kreini/J-r-s/PosTracker/Pályamunka/Grafikonok/Autokorreláció.docx

A képen képernyőkép, madár látható Automatikusan generált leírás
