kreini/J-r-s/PosTracker/Pályamunka/Grafikonok/Derék spline.docx

A képen képernyőkép látható Automatikusan generált leírás
