kreini/J-r-s/PosTracker/Pályamunka/Grafikonok/Nyers.docx

A képen képernyőkép látható Automatikusan generált leírás
A képen étel látható Automatikusan generált leírás
A képen képernyőkép látható Automatikusan generált leírás
