kreini/J-r-s/PosTracker/Pályamunka/Műszaki rajzok/Műszaki rajzok.docx

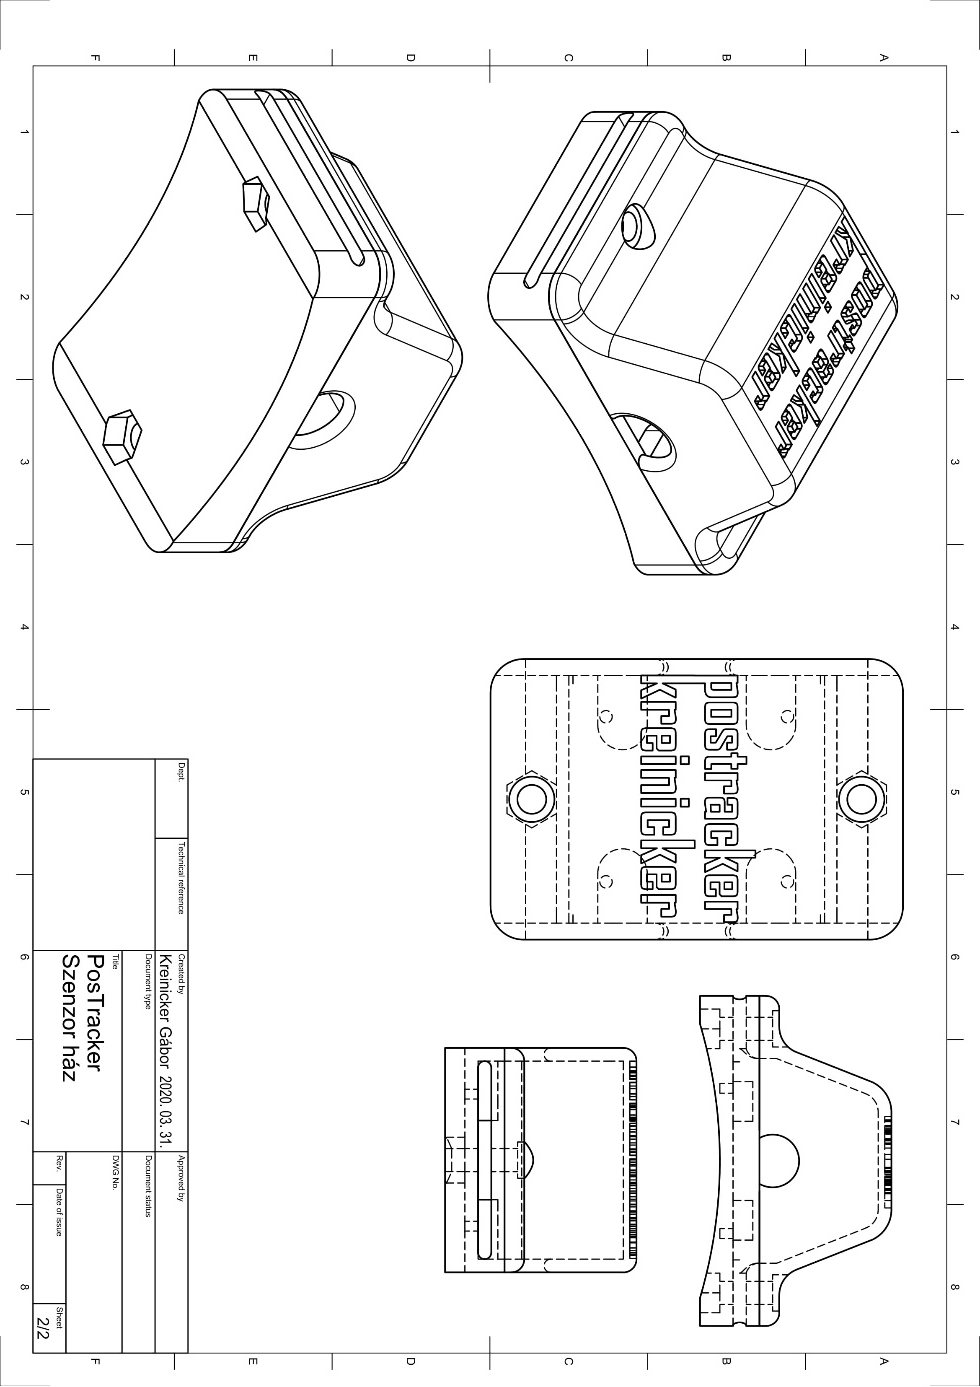
[picture p83: figure]
A képen szöveg, térkép látható Automatikusan generált leírás
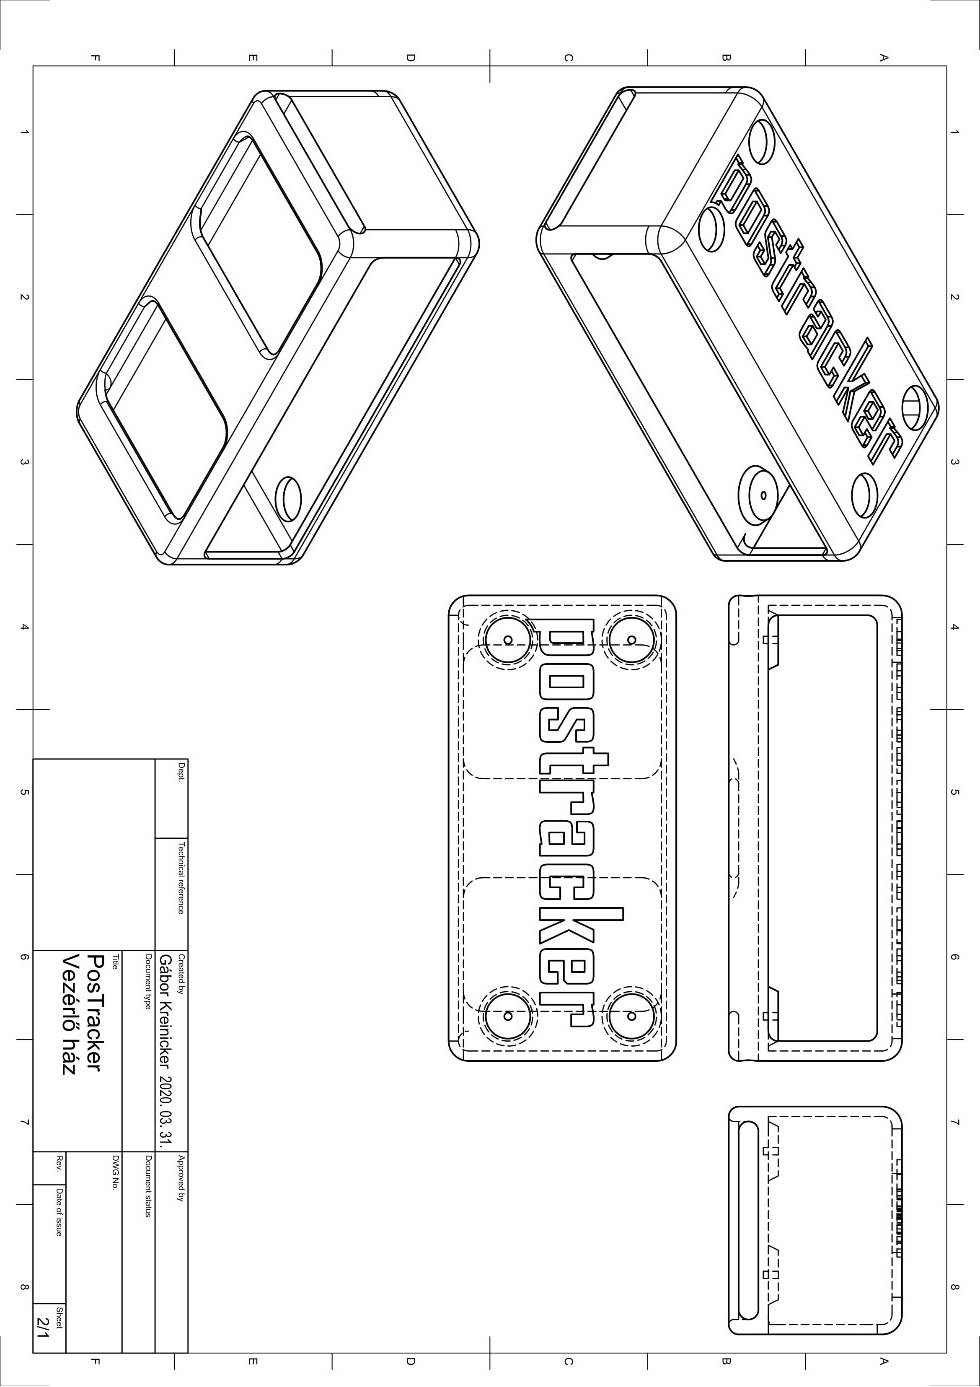
[picture p84: figure]
A képen szöveg, térkép, rajz látható Automatikusan generált leírás

A képen képernyőkép látható Automatikusan generált leírás
A képen étel látható Automatikusan generált leírás
A képen képernyőkép látható Automatikusan generált leírás

A képen képernyőkép látható Automatikusan generált leírás


A képen képernyőkép, madár látható Automatikusan generált leírás
