kreini/J-r-s/PosTracker/Pályamunka/Áramkör/Áramkör.docx

A képen szöveg, óra, nagyon nagy, fekete látható Automatikusan generált leírás
