kreini/J-r-s/pályázatok/JNEA/Igazolás.pdf

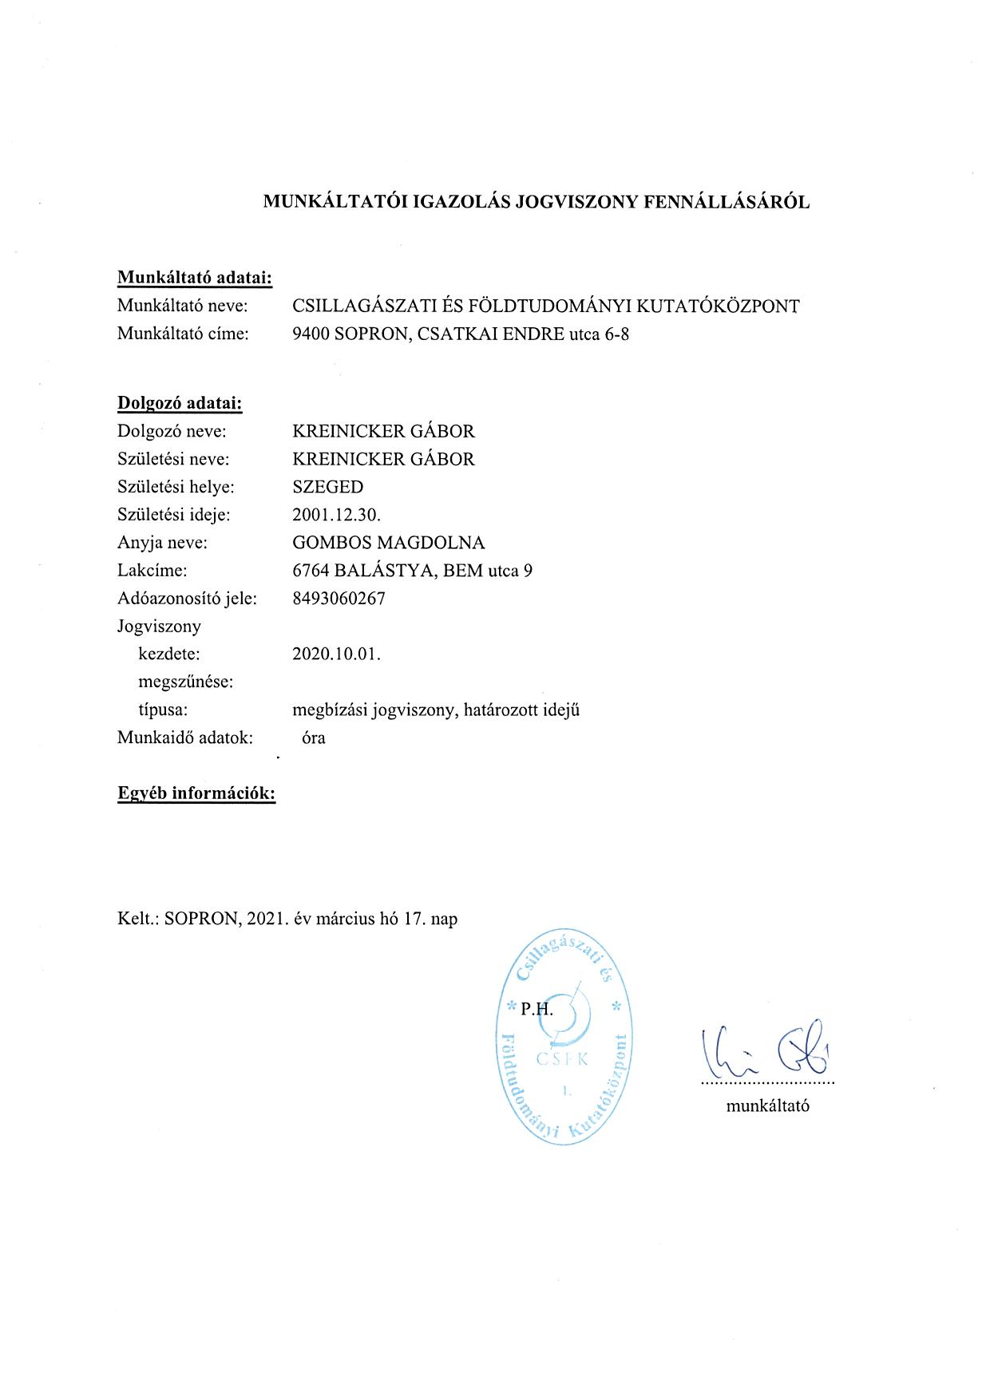
[picture p154: page 1]
