kreini/J-r-s/pályázatok/JNEA/Nyelvvizsga.pdf

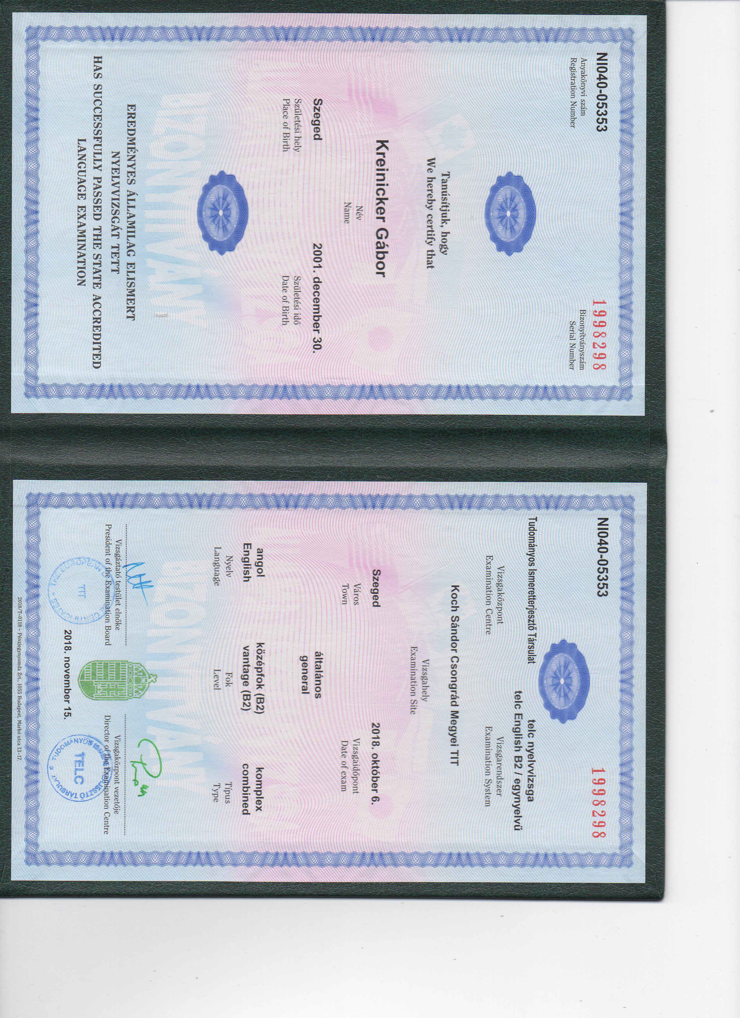
[picture p155: page 1]
