kreini/J-r-s/pályázatok/JNEA/Érettségi.pdf

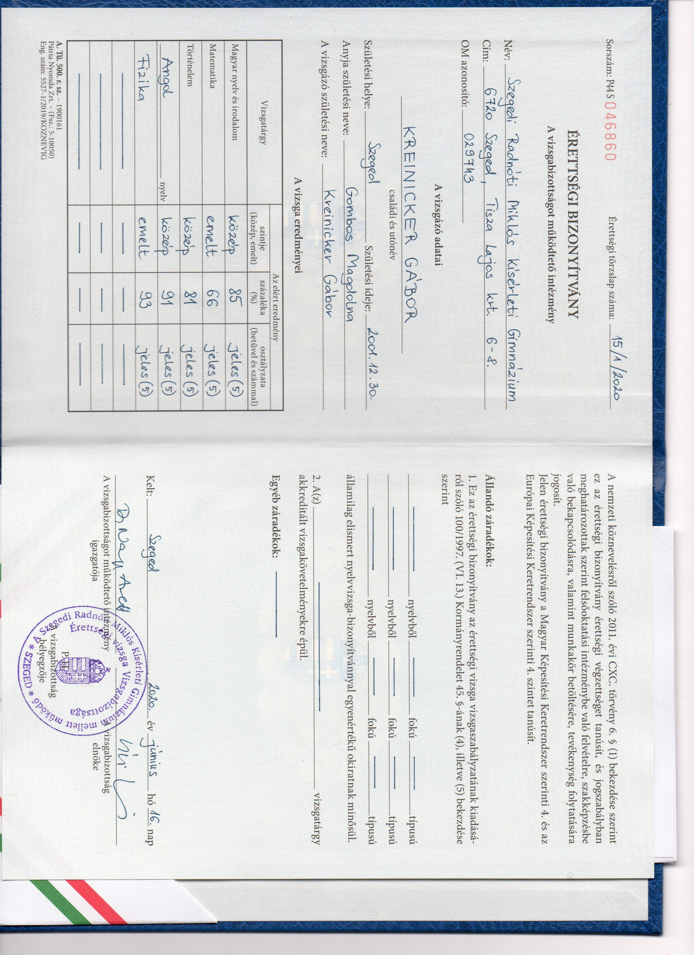
[picture p156: page 1]
