kreini/J-r-s/pályázatok/ÚNKP/2020-21/V_kutatási terv.pdf

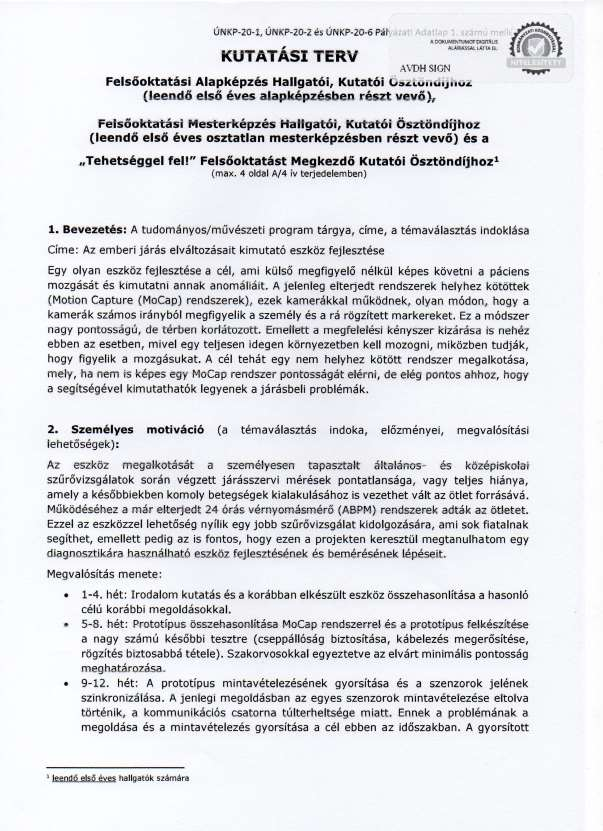
[picture p157: figure]

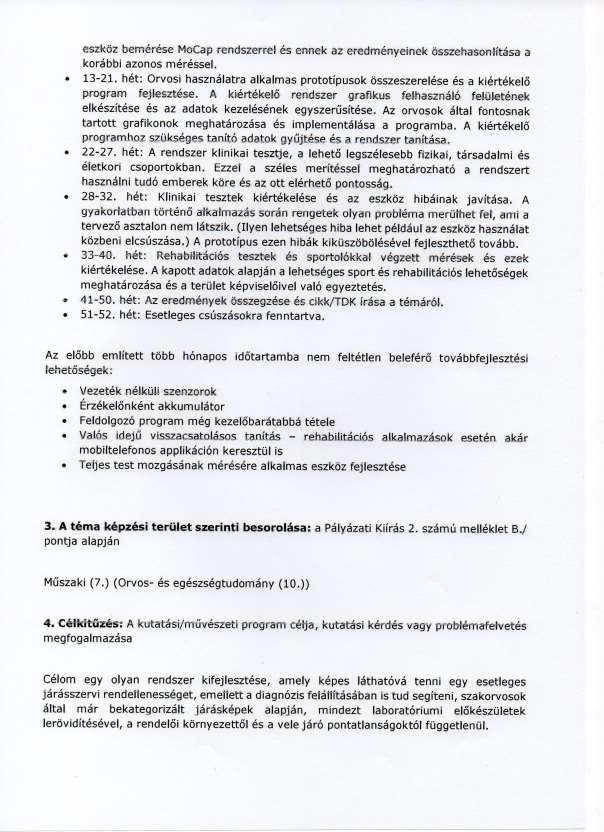
[picture p158: figure]

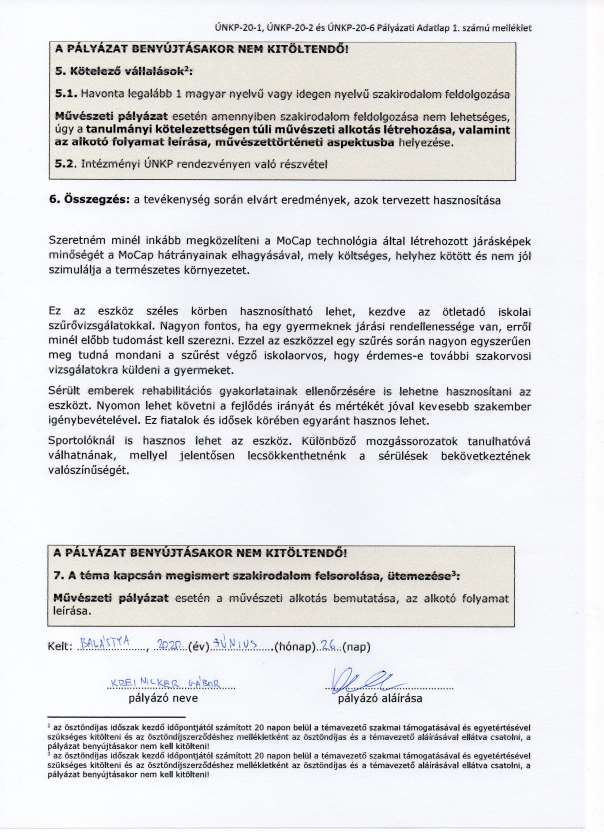
[picture p159: figure]
