kreini/J-r-s/pályázatok/ÚNKP/2020-21/V_pályázati adatlap.pdf

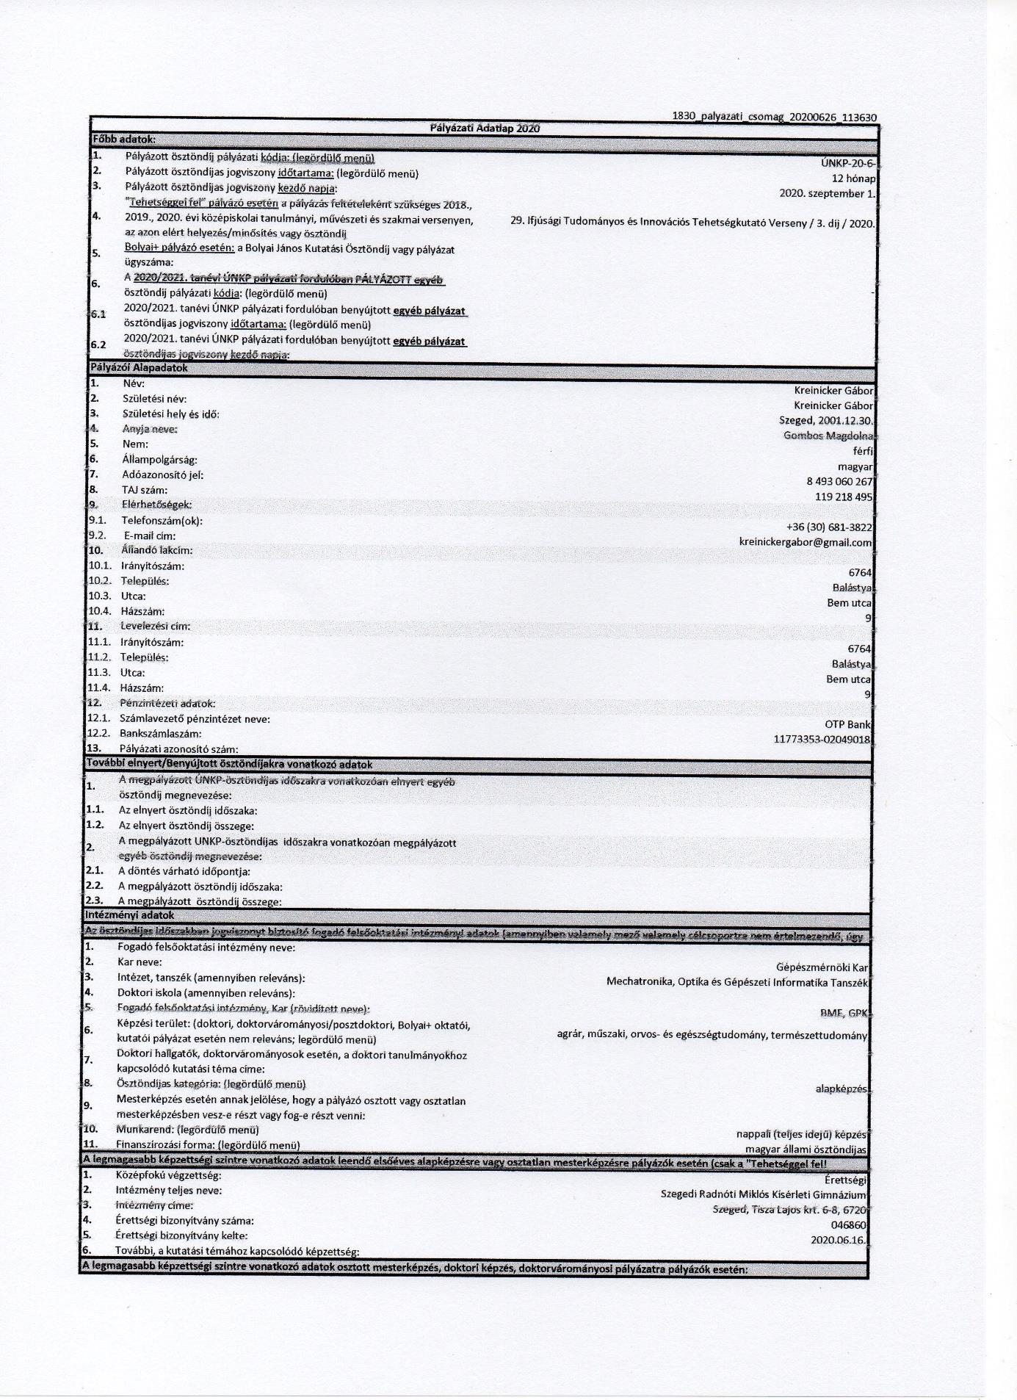
[picture p160: figure]

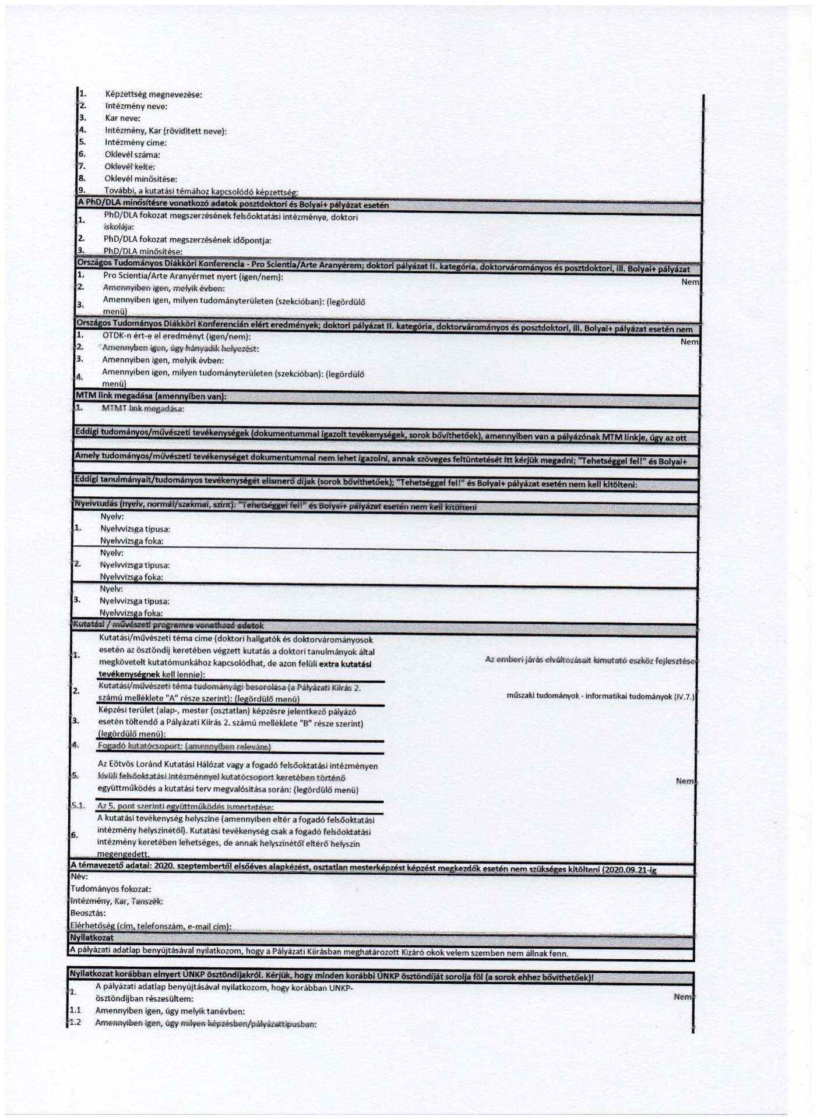
[picture p161: figure]

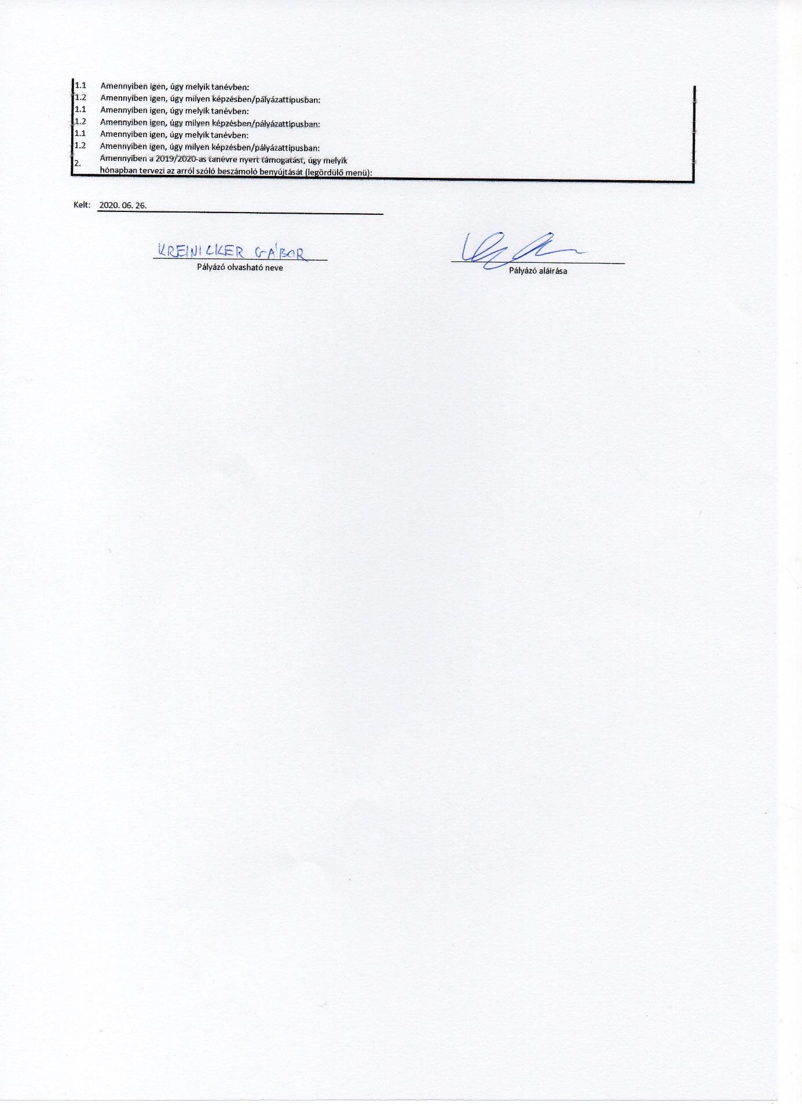
[picture p162: figure]
