kreini/J-r-s/pályázatok/ÚNKP/2020-21/V_pályázói nyilatkozat.pdf

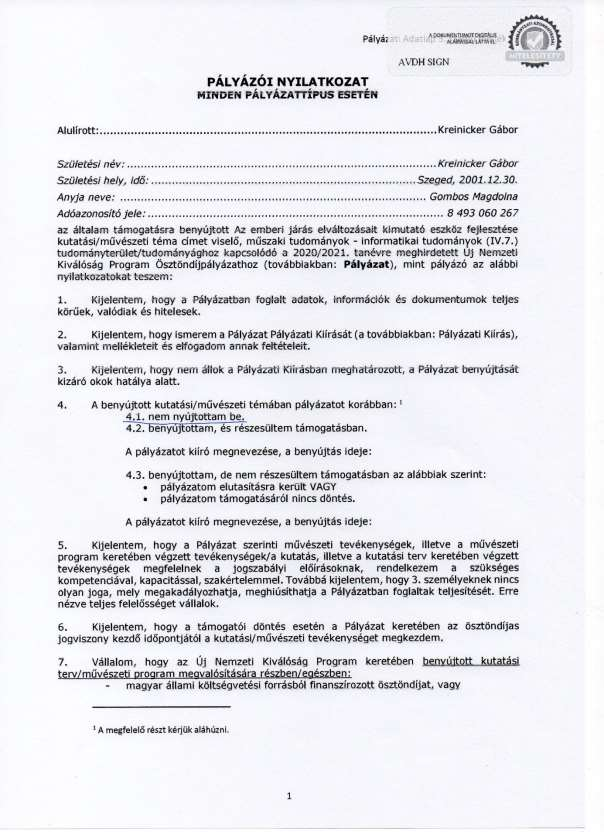
[picture p163: figure]

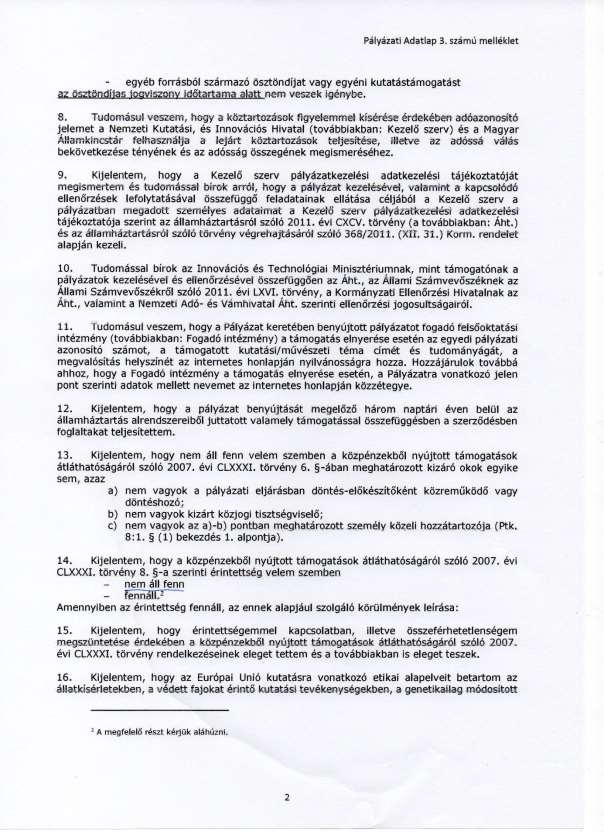
[picture p164: figure]

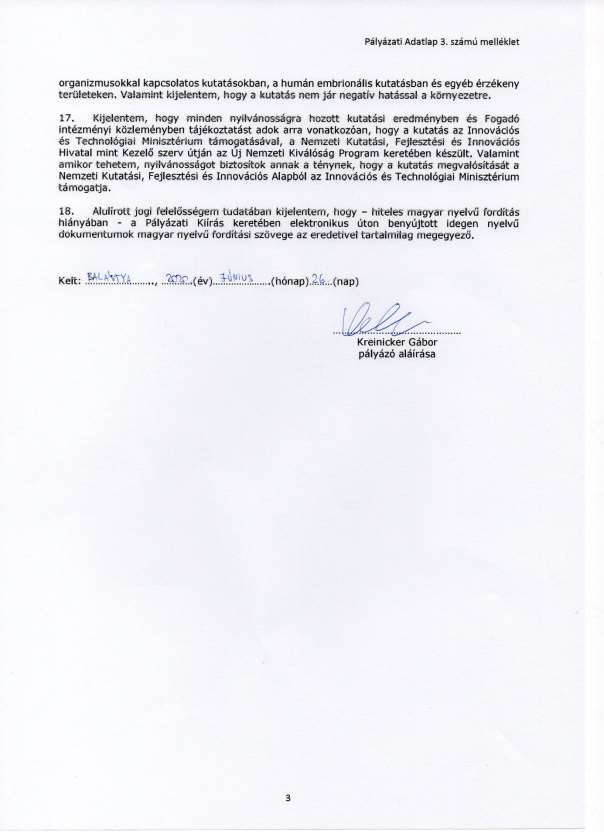
[picture p165: figure]
