kreini/J-r-s/pályázatok/ÚNKP/2020-21/V_versenyeredmény.pdf

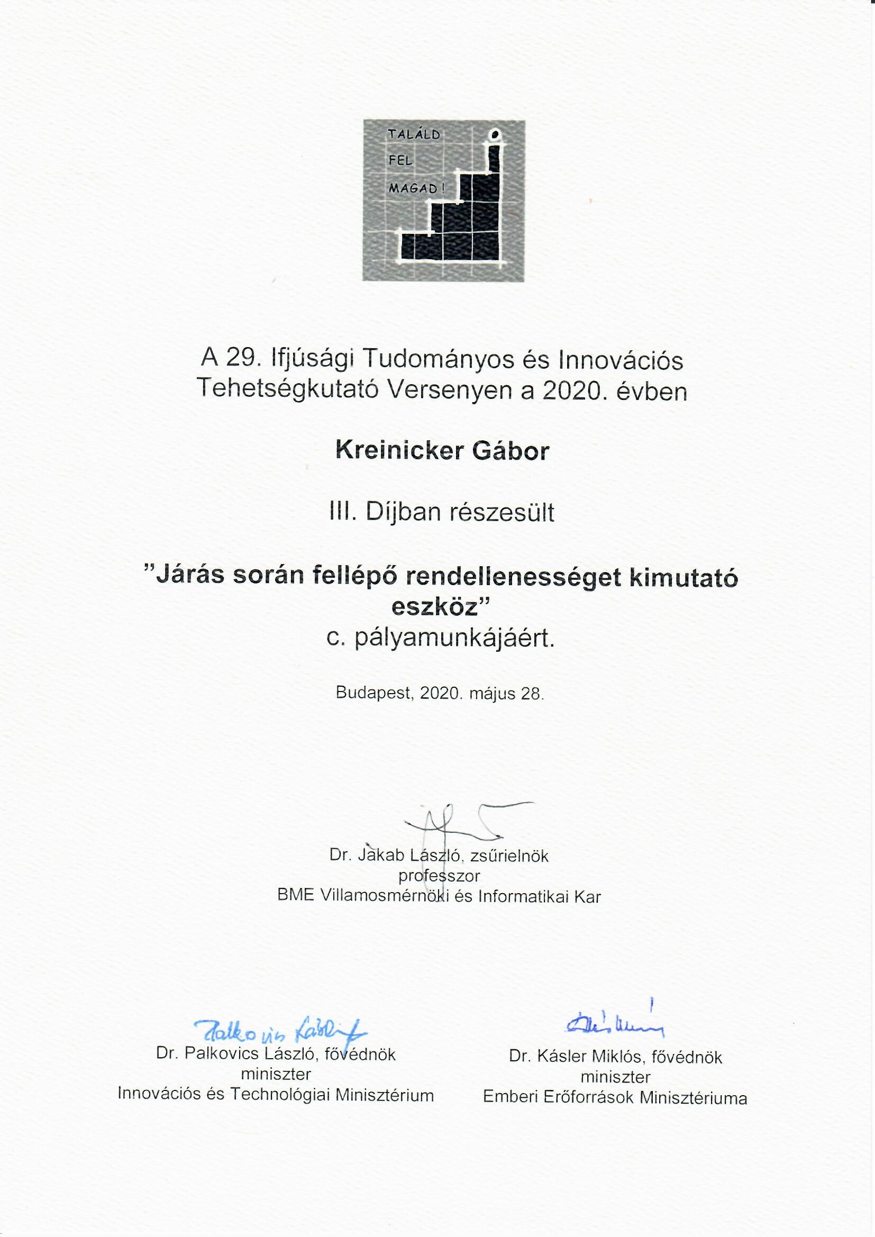
[picture p166: page 1]
