kreini/J-r-s/pályázatok/ÚNKP/2021-22/TDK.pdf

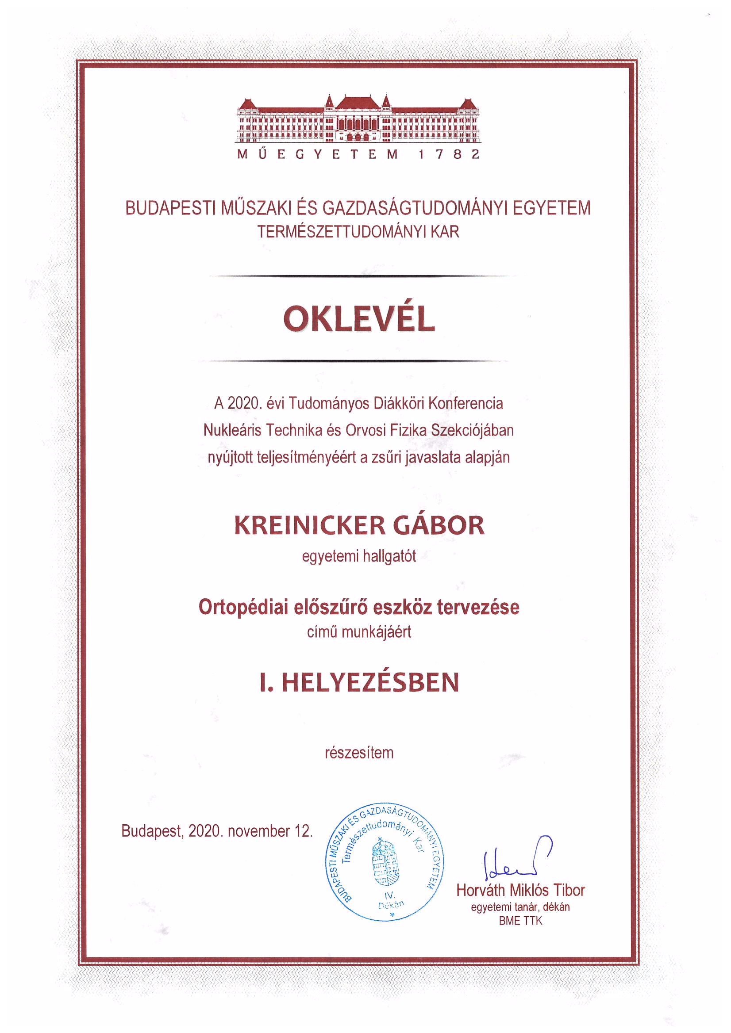
[picture p167: page 1]
