kreini/J-r-s/pályázatok/ÚNKP/2021-22/ÚNKP - GSZK - Kreinicker-Gábor_aláírt_RK.pdf

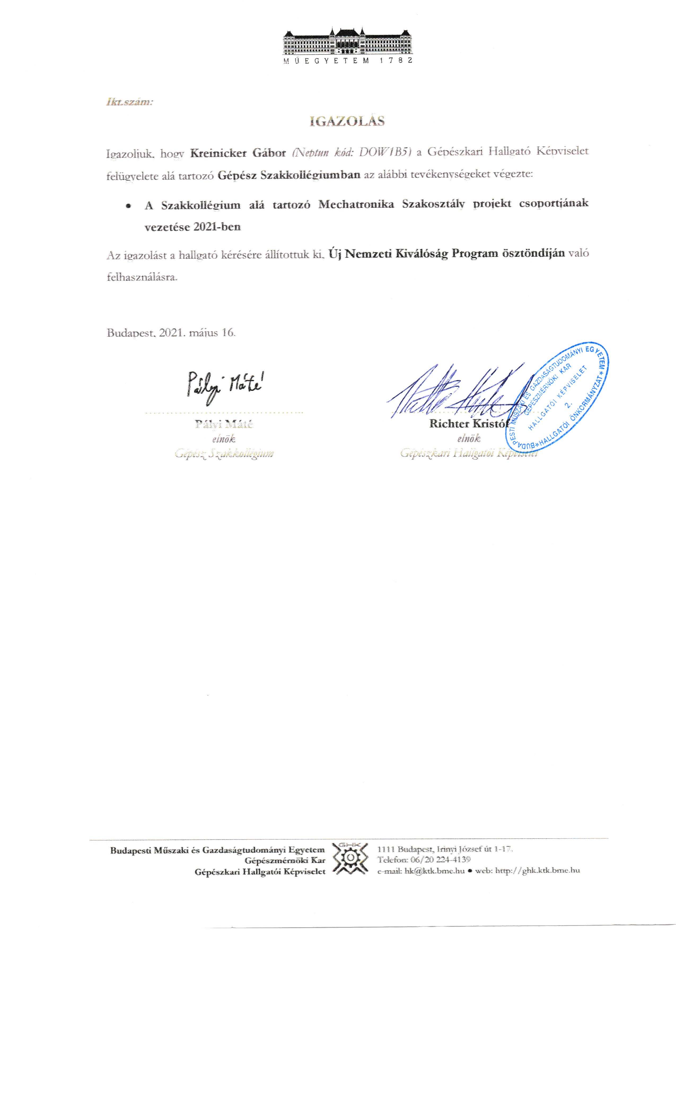
[picture p168: page 1]
