kreini/J-r-s/PosTracker/Kiselőadás/Háttérképek/1.1.jpg

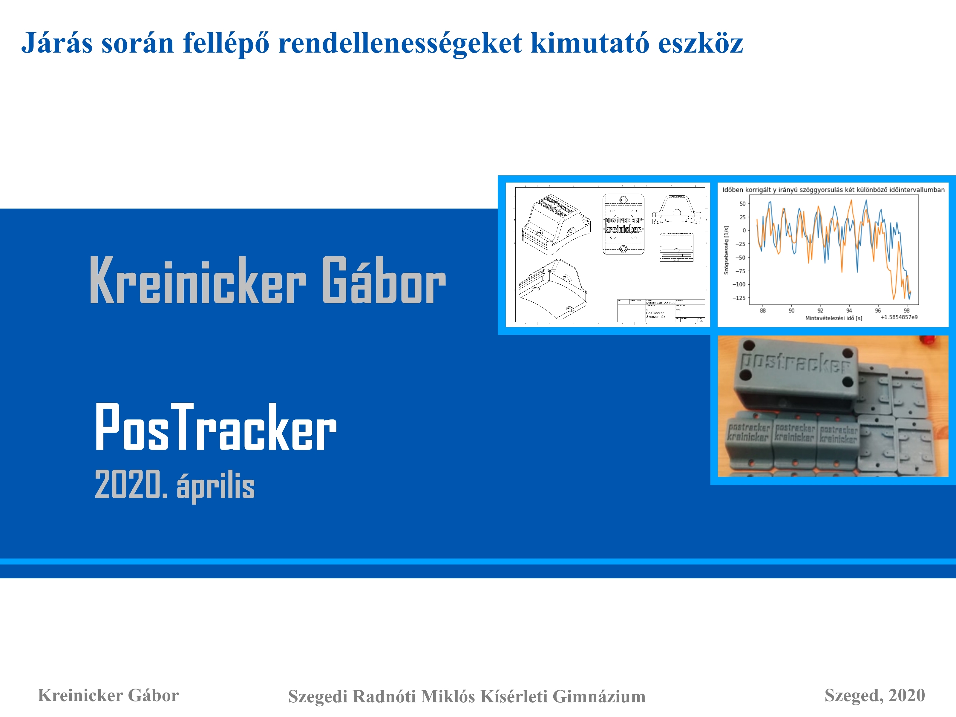
PosTracker/Kiselőadás/Háttérképek/1.1.jpg
