kreini/J-r-s/PosTracker/Kiselőadás/Háttérképek/2-6.jpg

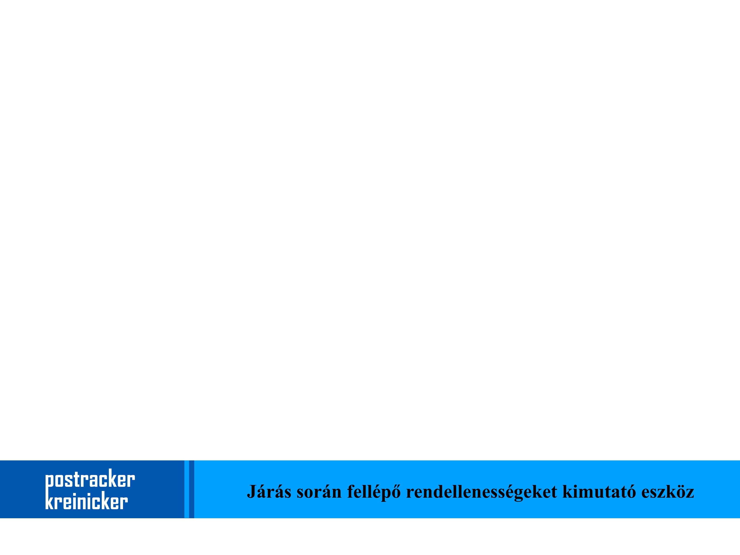
PosTracker/Kiselőadás/Háttérképek/2-6.jpg
