kreini/J-r-s/PosTracker/Mérések/1 - Gábor - siker/1 - Gábor.png

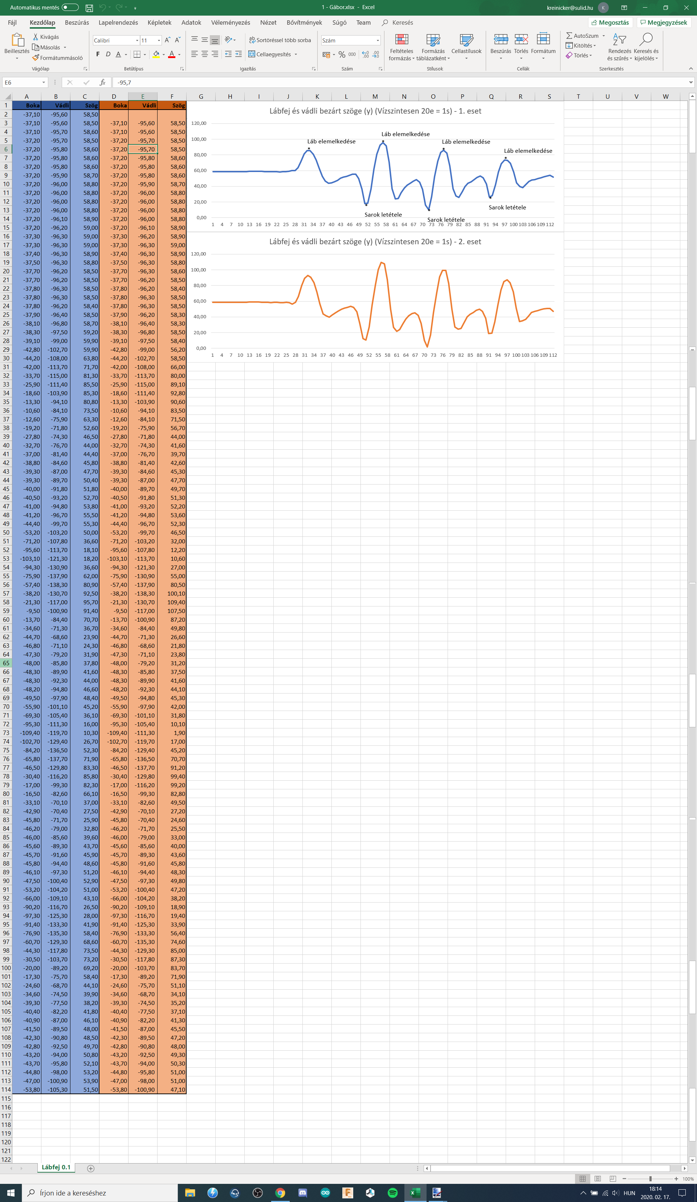
PosTracker/Mérések/1 - Gábor - siker/1 - Gábor.png
