kreini/J-r-s/PosTracker/Pályamunka/Grafikonok/Tánc/Küküllőmenti pontozó 2.JPG

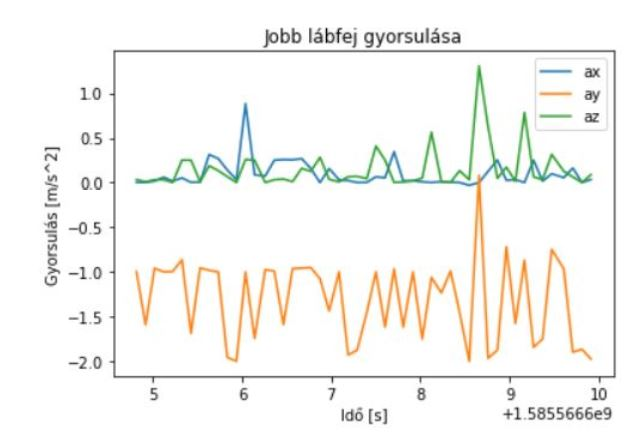
PosTracker/Pályamunka/Grafikonok/Tánc/Küküllőmenti pontozó 2.JPG
