kreini/J-r-s/PosTracker/Pályamunka/Grafikonok/Tánc/Küküllőmenti pontozó.JPG

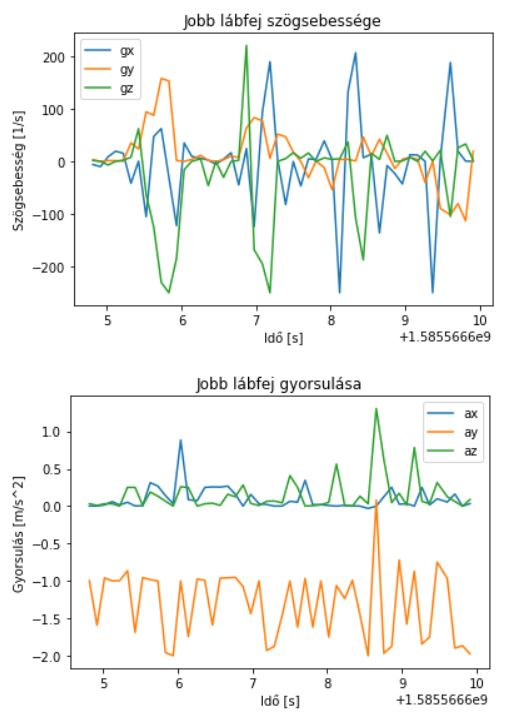
PosTracker/Pályamunka/Grafikonok/Tánc/Küküllőmenti pontozó.JPG
