kreini/J-r-s/PosTracker/Pályamunka/Grafikonok/Tánc/Mezőségi korcsos 2.JPG

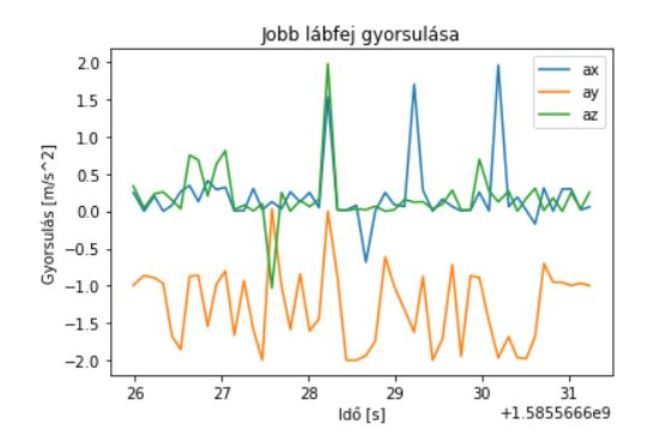
PosTracker/Pályamunka/Grafikonok/Tánc/Mezőségi korcsos 2.JPG
