kreini/J-r-s/PosTracker/Pályamunka/Grafikonok/Tánc/Mezőségi korcsos.JPG

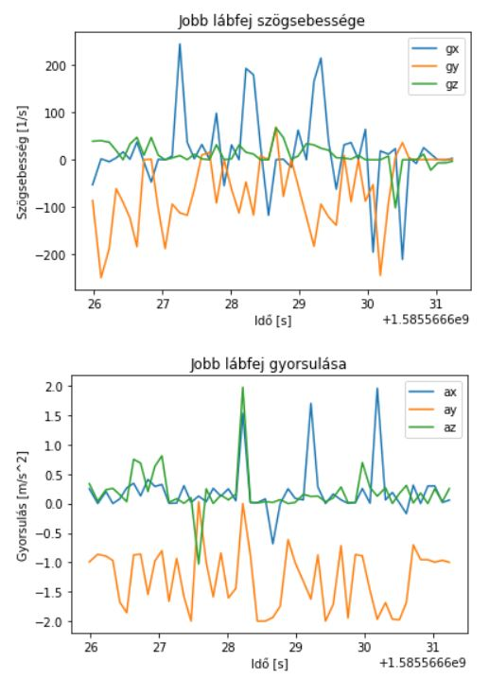
PosTracker/Pályamunka/Grafikonok/Tánc/Mezőségi korcsos.JPG
