kreini/J-r-s/PosTracker/Videó/Index.png

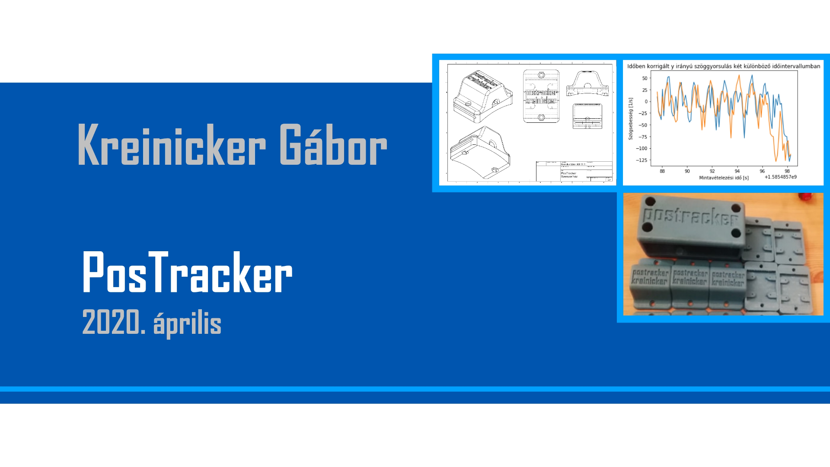
PosTracker/Videó/Index.png
