kreini/J-r-s/PosTracker/Videó/Nyers képek/IMG_20200328_200417.jpg

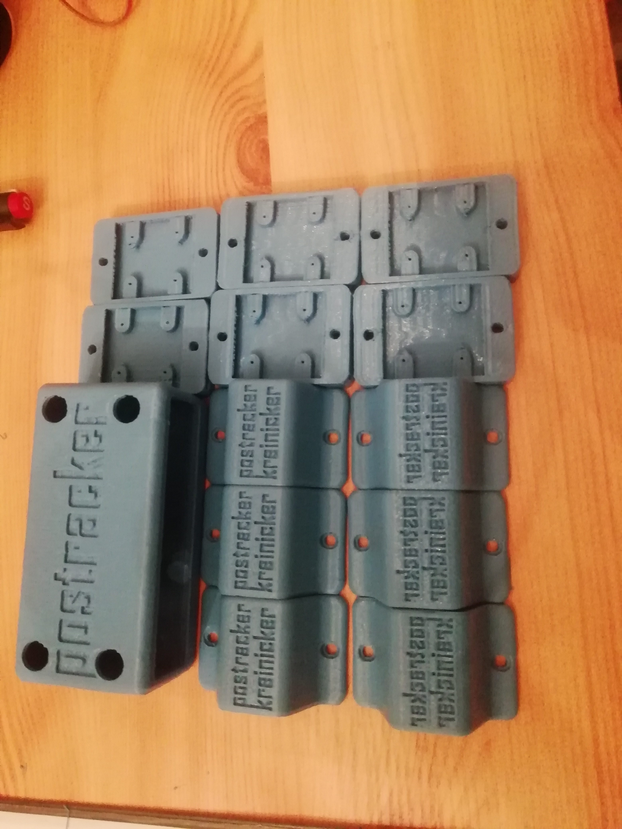
PosTracker/Videó/Nyers képek/IMG_20200328_200417.jpg
