kreini/J-r-s/PosTracker/Videó/Nyers képek/IMG_20200330_115611.jpg

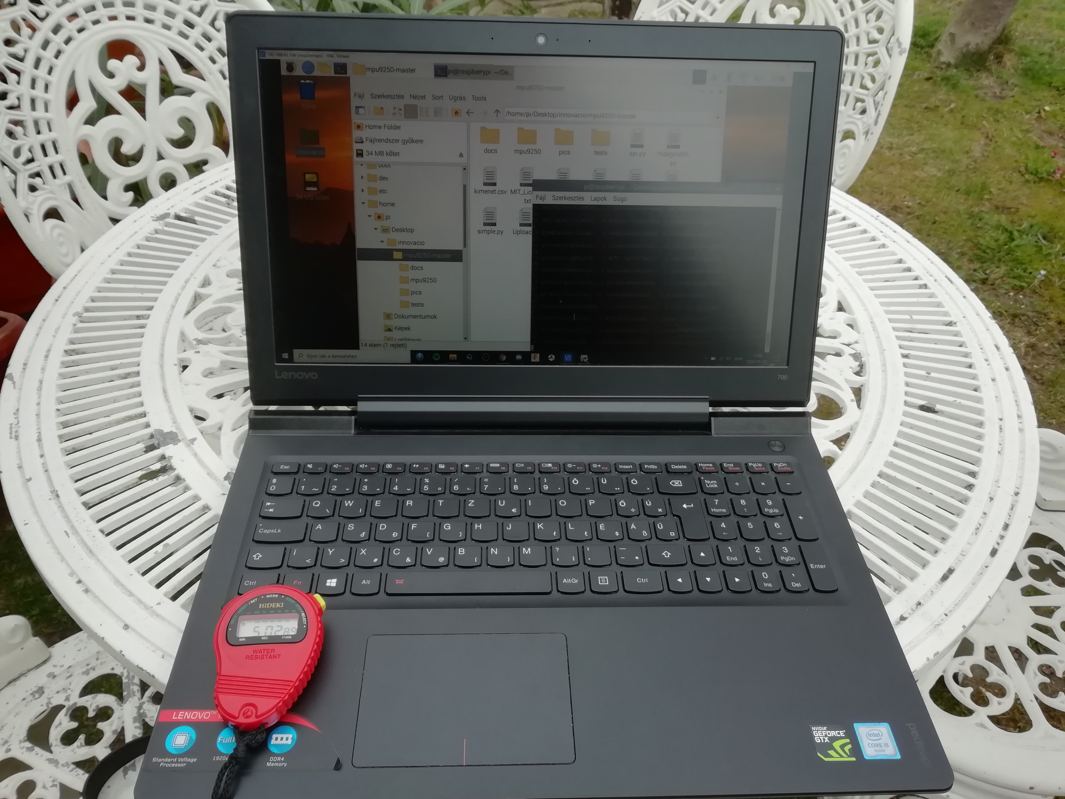
PosTracker/Videó/Nyers képek/IMG_20200330_115611.jpg
