kreini/J-r-s/PosTracker/Videó/Nyers képek/IMG_20200410_112839.jpg

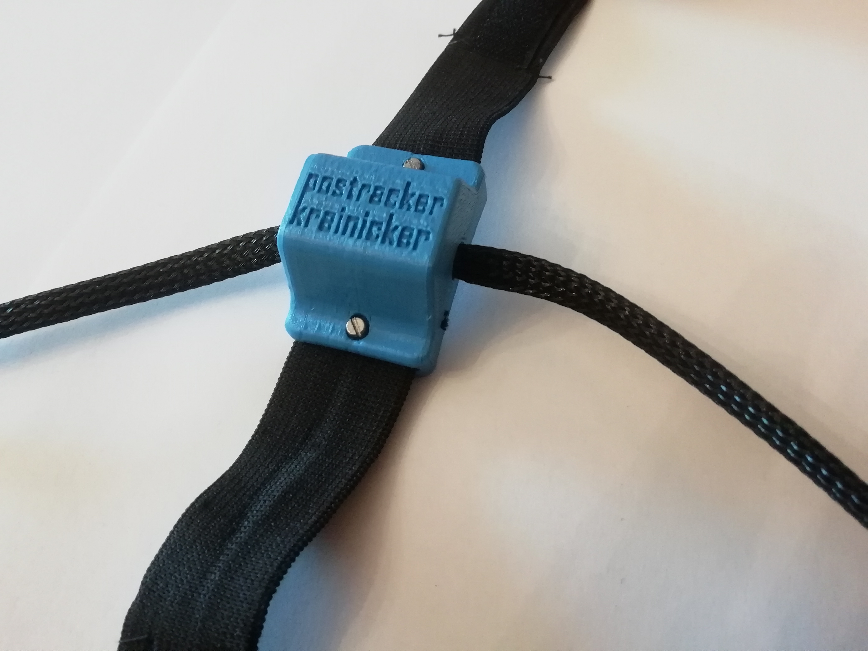
PosTracker/Videó/Nyers képek/IMG_20200410_112839.jpg
