kreini/J-r-s/PosTracker/Videó/Nyers képek/IMG_20200410_143606.jpg

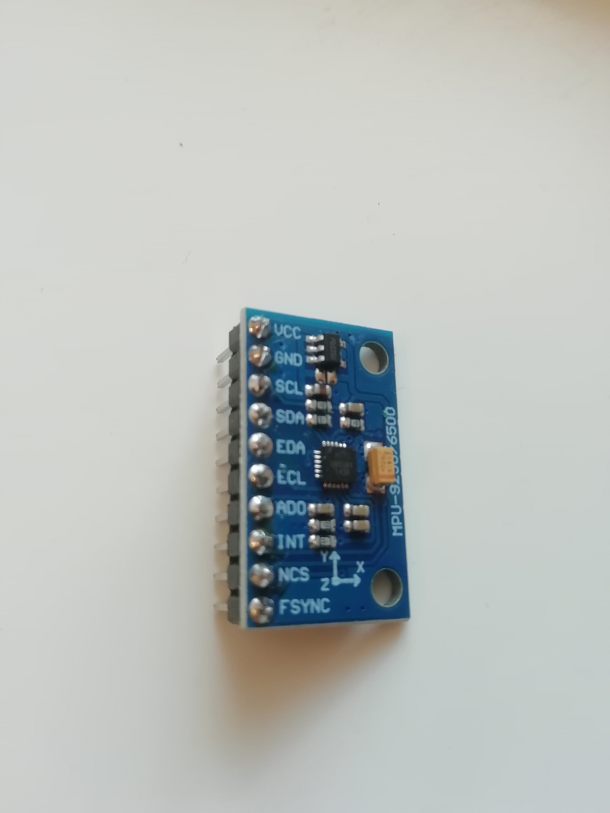
PosTracker/Videó/Nyers képek/IMG_20200410_143606.jpg
