kreini/J-r-s/PosTracker/Videó/Nyers képek/IMG_20200410_144037.jpg

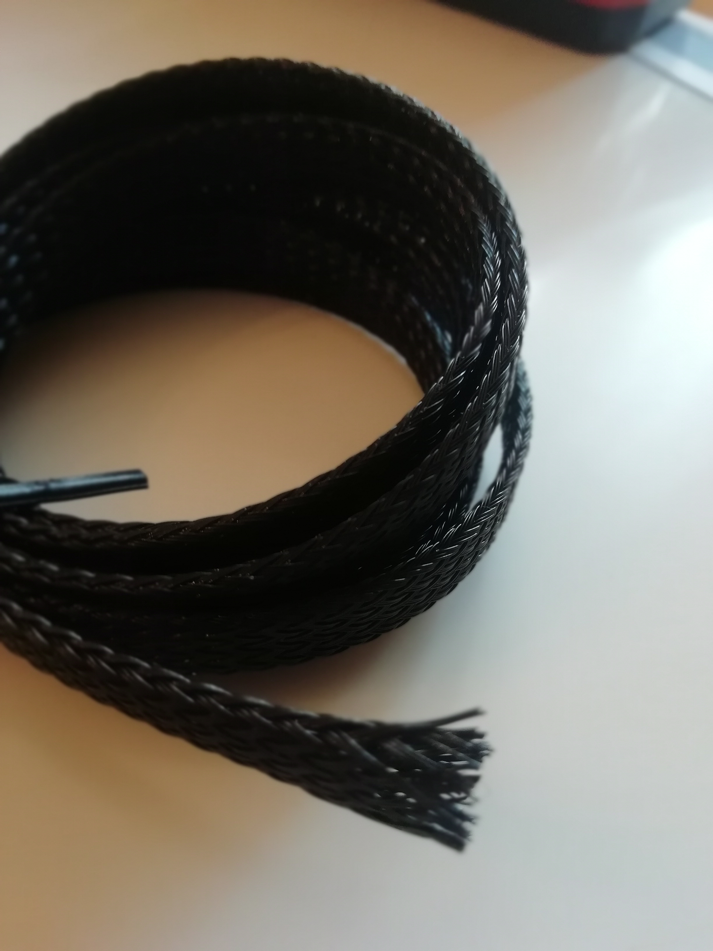
PosTracker/Videó/Nyers képek/IMG_20200410_144037.jpg
