kreini/J-r-s/PosTracker/Videó/Nyers képek/Kép1.jpg

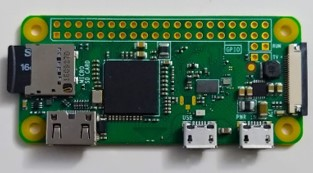
PosTracker/Videó/Nyers képek/Kép1.jpg
