kreini/J-r-s/PosTracker/Videó/Nyers képek/Kép2.jpg

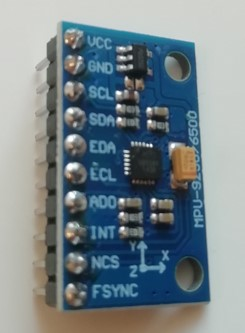
PosTracker/Videó/Nyers képek/Kép2.jpg
