kreini/J-r-s/PosTracker/Videó/Nyers képek/Kép4.jpg

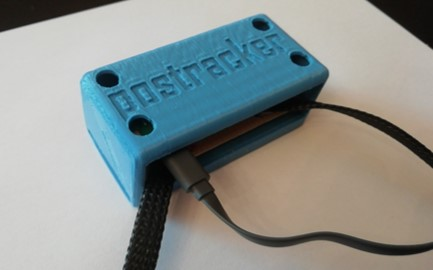
PosTracker/Videó/Nyers képek/Kép4.jpg
