kreini/J-r-s/PosTracker/Videó/Nyers képek/Kör.png

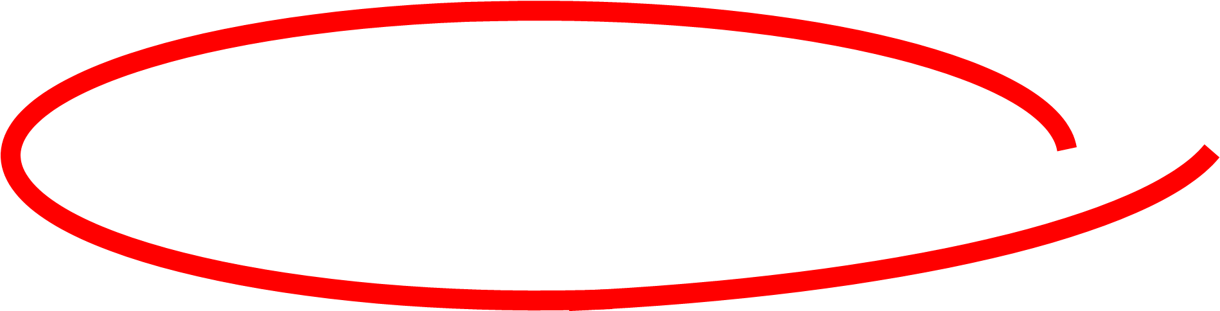
PosTracker/Videó/Nyers képek/Kör.png
