kreini/J-r-s/PosTracker/Videó/Nyers képek/Nyíl.png

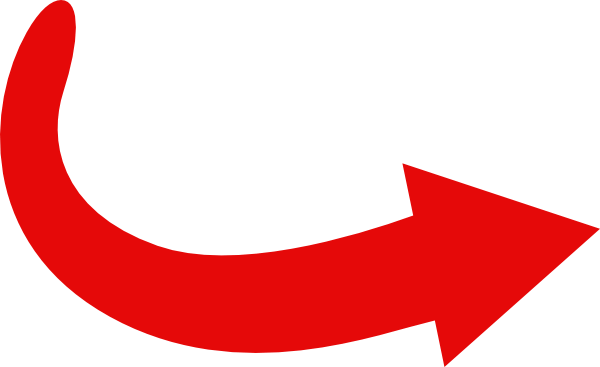
PosTracker/Videó/Nyers képek/Nyíl.png
