kreini/J-r-s/pályázatok/InnoGEN 2021/InnoGEN.jpg

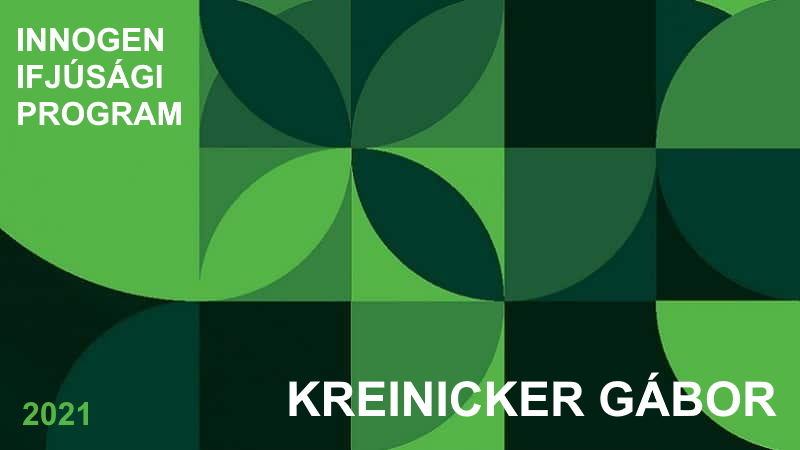
pályázatok/InnoGEN 2021/InnoGEN.jpg
