kreini/J-r-s/TDK 2020/Dokumentumok/f47b5ffb-0a47-4b73-9f30-1225e2438b1b.png

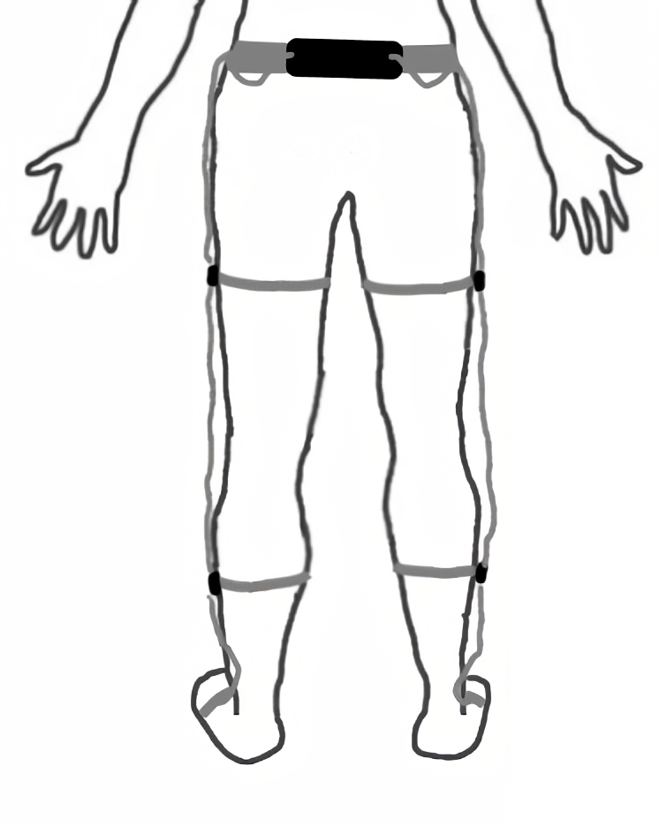
TDK 2020/Dokumentumok/f47b5ffb-0a47-4b73-9f30-1225e2438b1b.png
