kreini/J-r-s/TDK 2020/Dokumentumok/IMG_20201028_184122.jpg

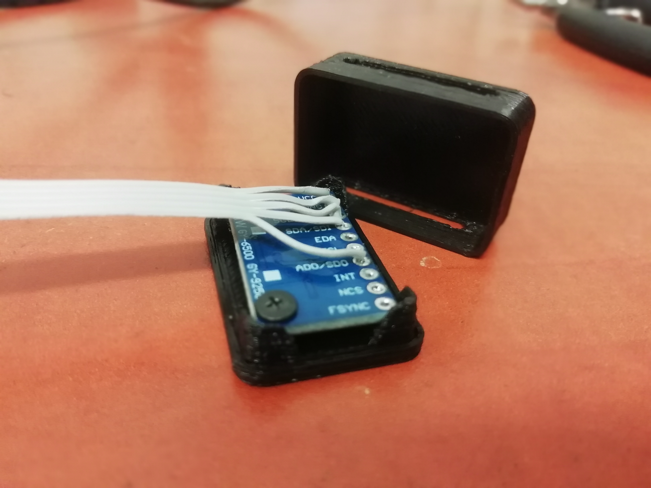
TDK 2020/Dokumentumok/IMG_20201028_184122.jpg
