kreini/J-r-s/TDK 2020/Kiselőadás/Kreinicker Gábor.jpg

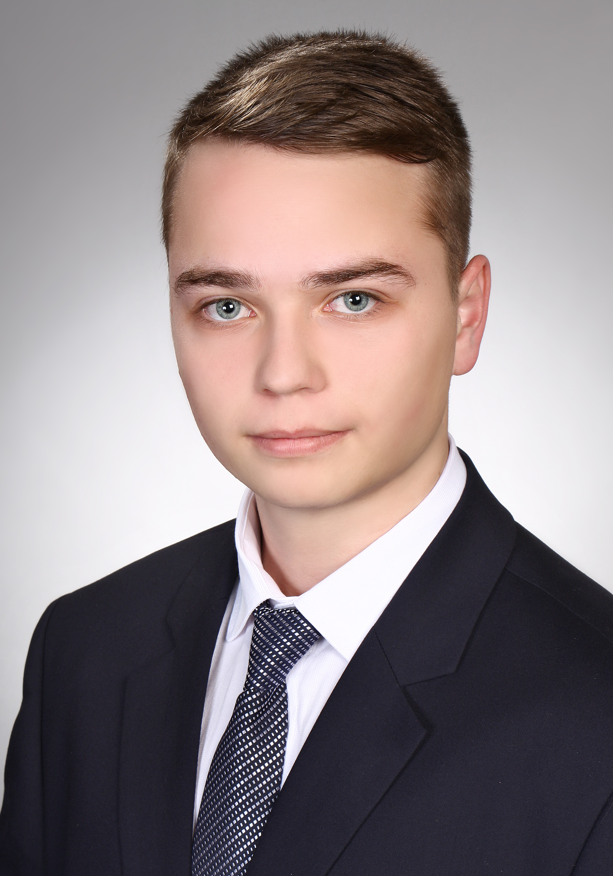
TDK 2020/Kiselőadás/Kreinicker Gábor.jpg
