kreini/J-r-s/TDK 2021/Képek/azonos.png

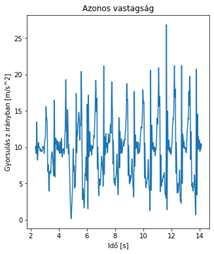
TDK 2021/Képek/azonos.png
