kreini/J-r-s/TDK 2021/Képek/Baszó.png

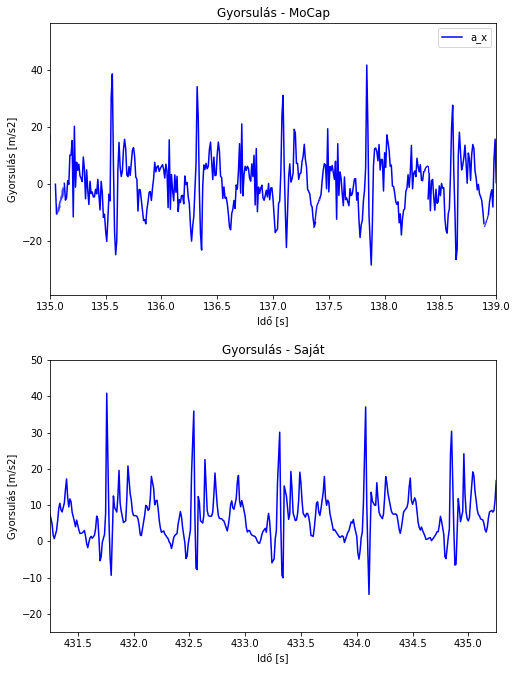
TDK 2021/Képek/Baszó.png
