kreini/J-r-s/TDK 2021/Képek/Bicepsz.png

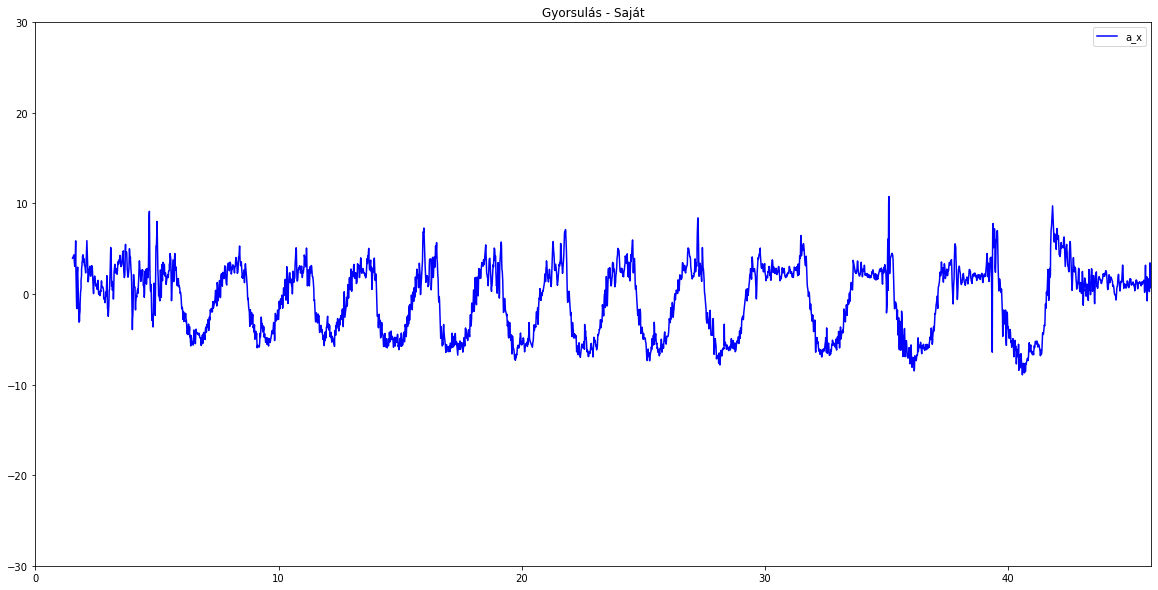
TDK 2021/Képek/Bicepsz.png
