kreini/J-r-s/TDK 2021/Képek/Bicepsz_1.png

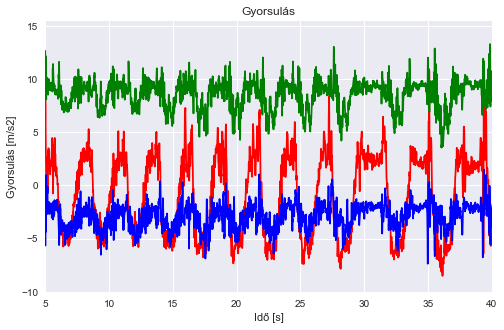
TDK 2021/Képek/Bicepsz_1.png
