kreini/J-r-s/TDK 2021/Képek/Bicepsz_2.png

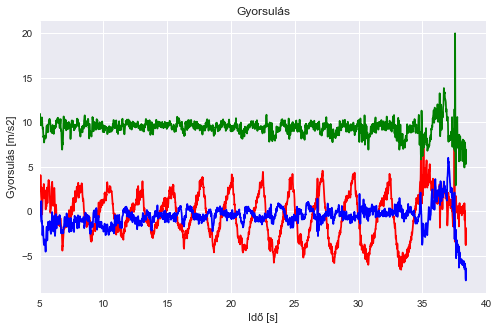
TDK 2021/Képek/Bicepsz_2.png
