kreini/J-r-s/TDK 2021/Képek/Bicepsz_2_korr.png

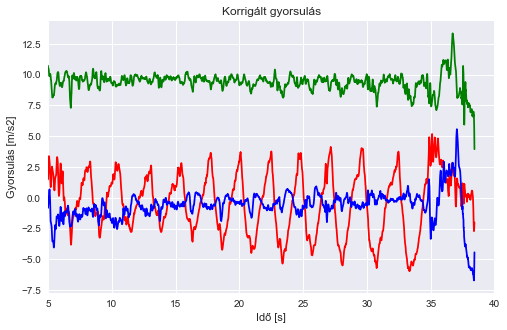
TDK 2021/Képek/Bicepsz_2_korr.png
