kreini/J-r-s/TDK 2021/Képek/IMG_20211020_145517.jpg

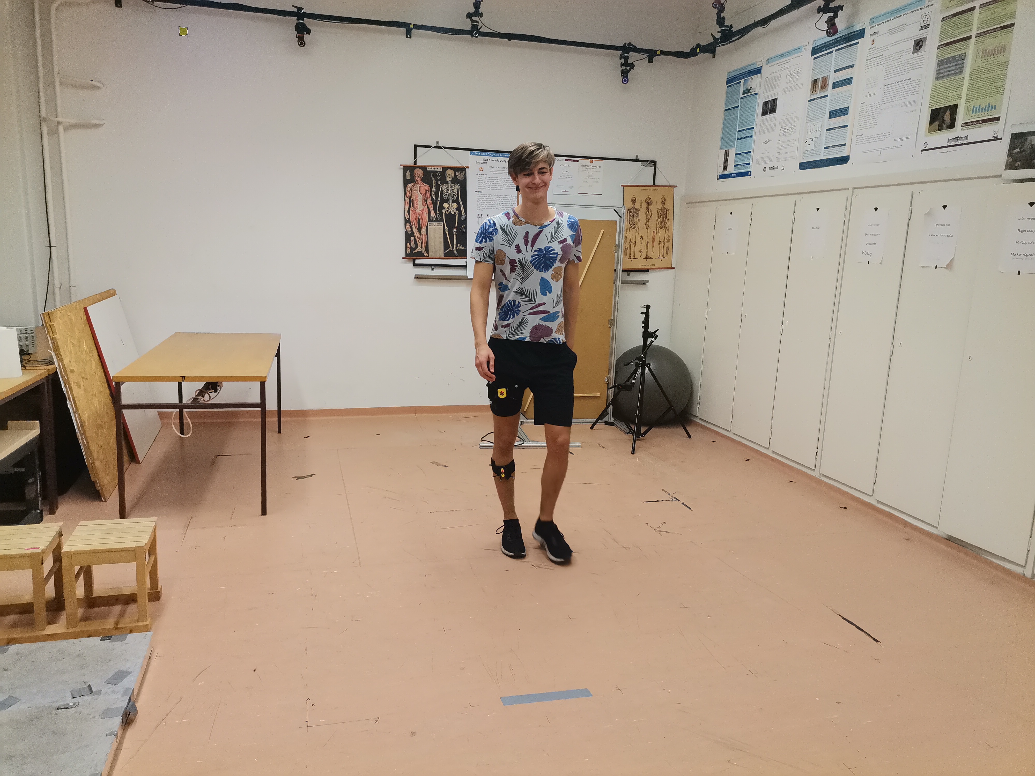
TDK 2021/Képek/IMG_20211020_145517.jpg
