kreini/J-r-s/TDK 2021/Képek/IMG_20211020_160707.jpg

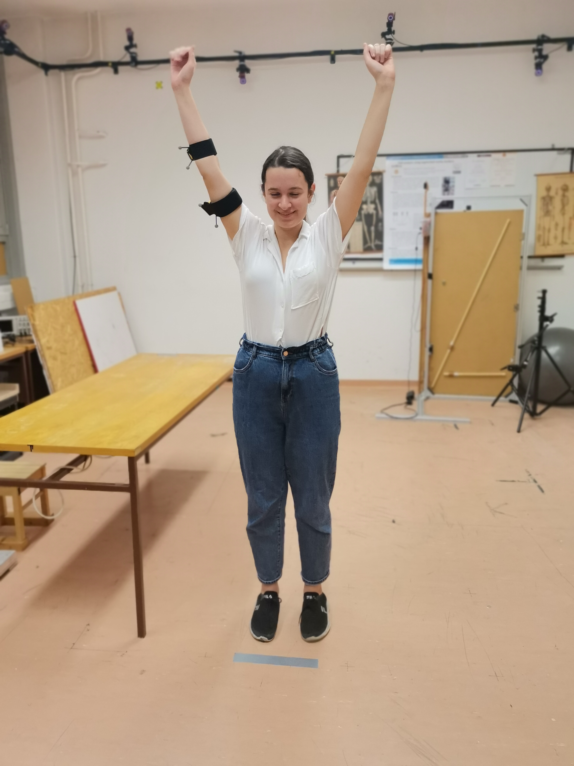
TDK 2021/Képek/IMG_20211020_160707.jpg
