kreini/J-r-s/TDK 2021/Képek/IMG_20211020_170008.jpg

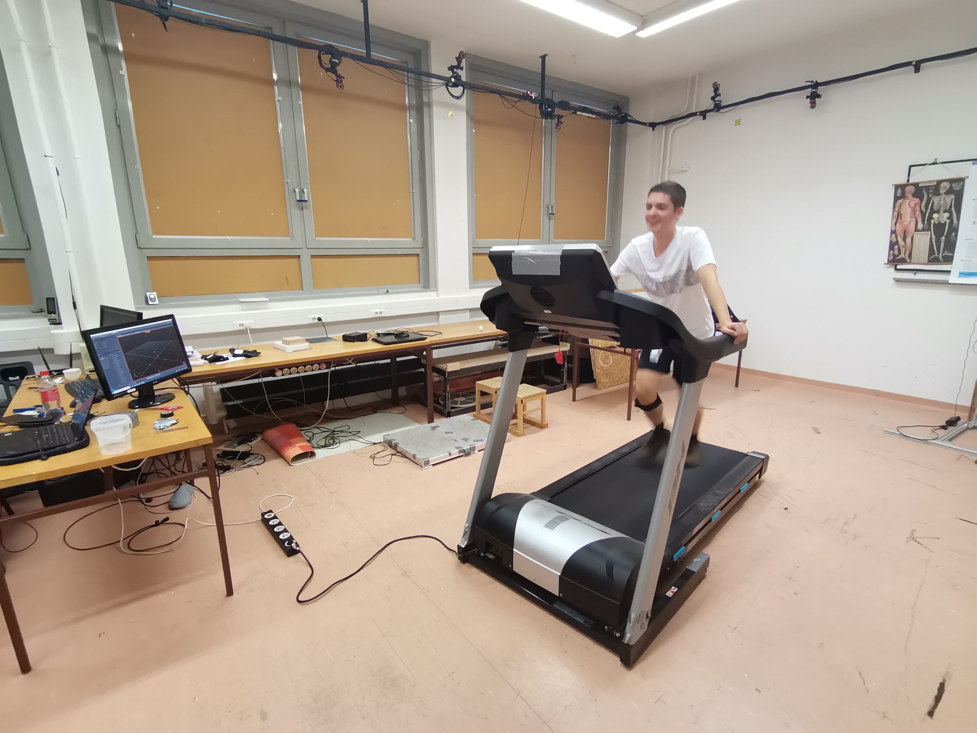
TDK 2021/Képek/IMG_20211020_170008.jpg
