kreini/J-r-s/TDK 2021/Képek/lakmax.png

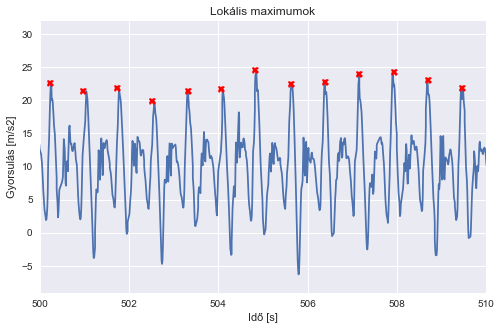
TDK 2021/Képek/lakmax.png
