kreini/J-r-s/TDK 2021/Képek/MoCap.gif

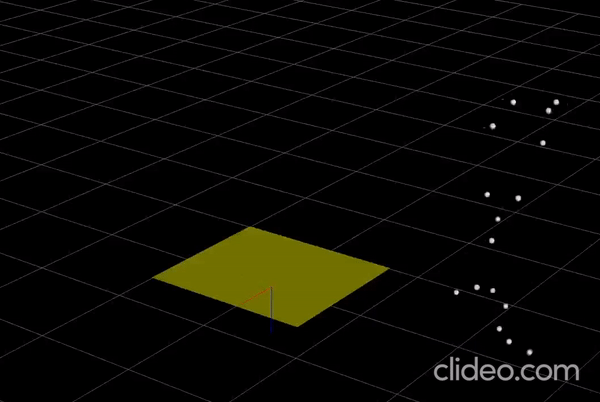
TDK 2021/Képek/MoCap.gif
