kreini/J-r-s/TDK 2021/Képek/MoCap.png

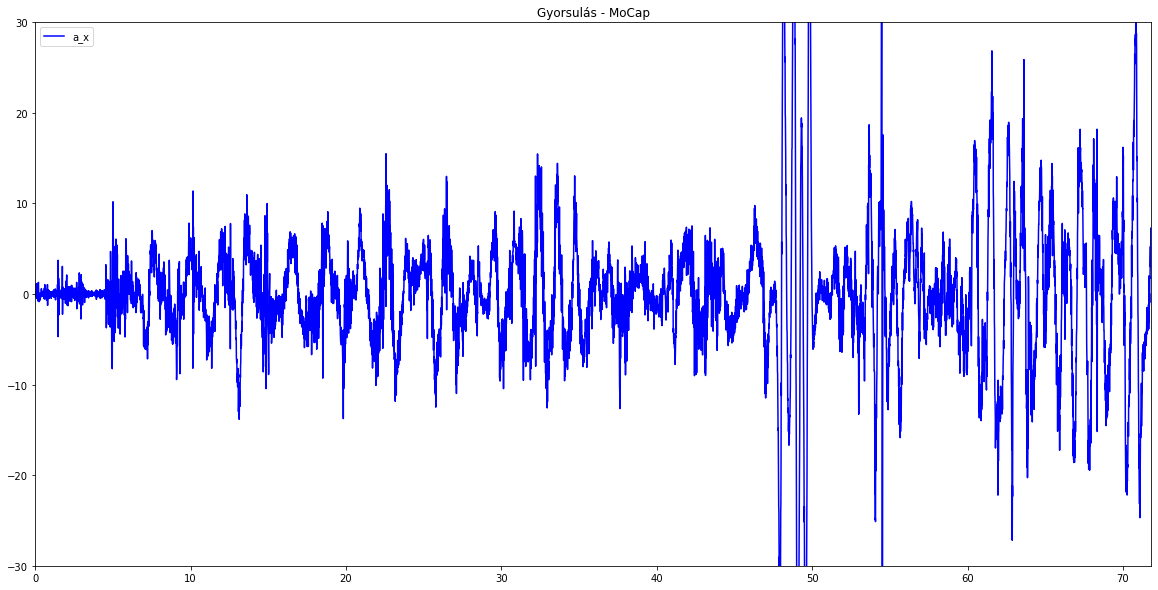
TDK 2021/Képek/MoCap.png
