kreini/J-r-s/TDK 2021/Képek/MoCap_Akos.png

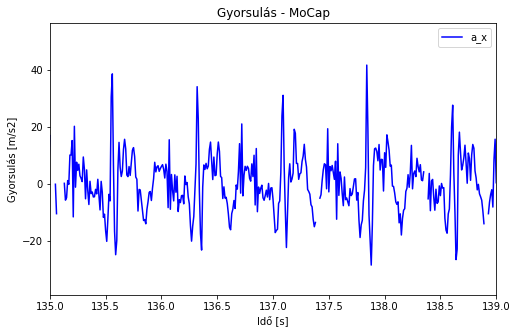
TDK 2021/Képek/MoCap_Akos.png
