kreini/J-r-s/TDK 2021/Képek/Sajat.png

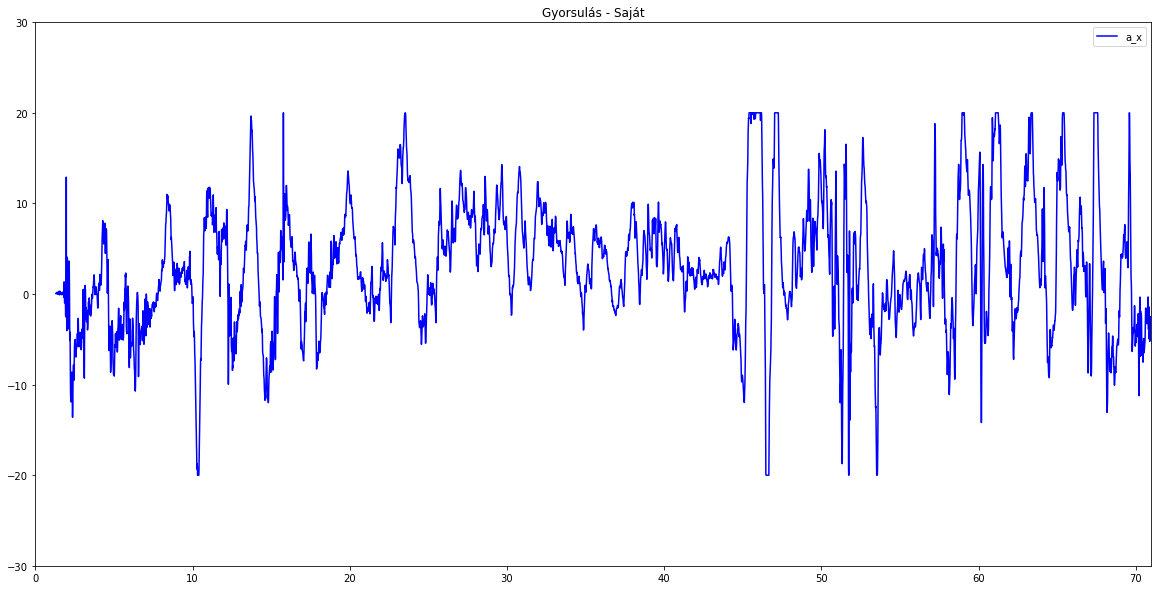
TDK 2021/Képek/Sajat.png
