kreini/J-r-s/TDK 2021/Képek/Sajat_Akos.png

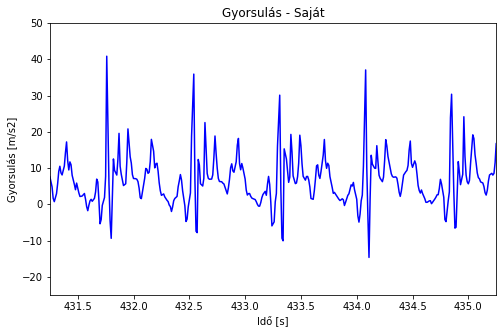
TDK 2021/Képek/Sajat_Akos.png
