kreini/J-r-s/TDK 2021/Nyákterv/Jaras_nyak_1.png

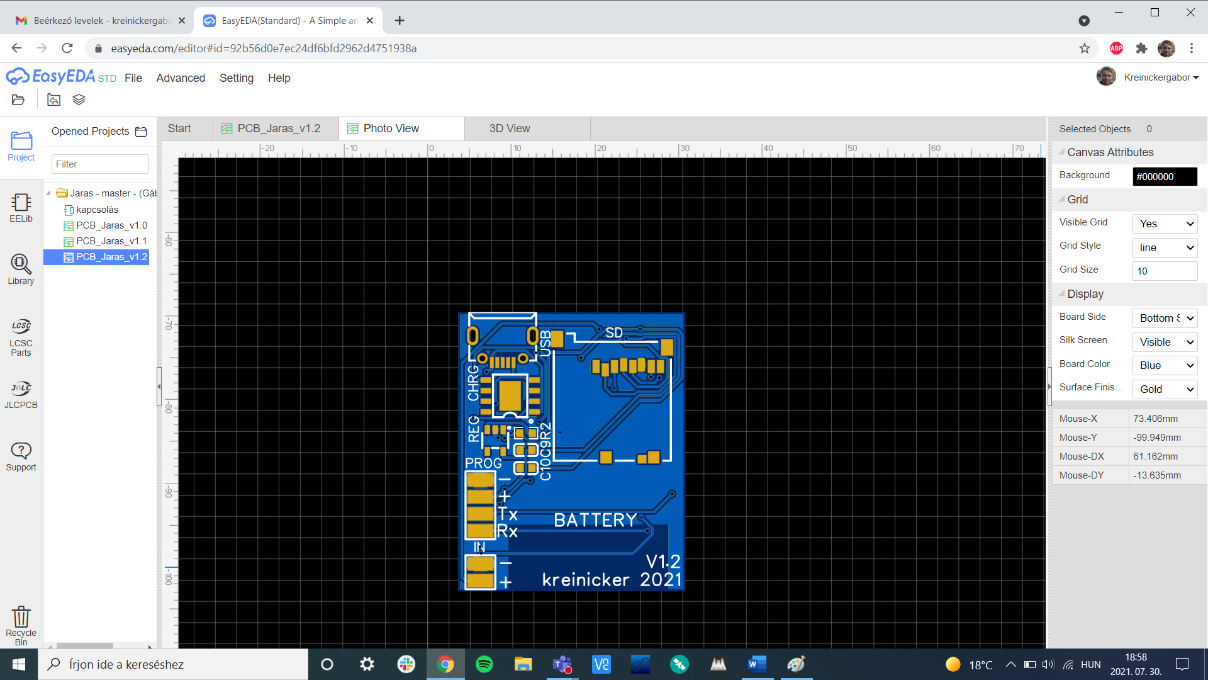
TDK 2021/Nyákterv/Jaras_nyak_1.png
