kreini/J-r-s/TDK 2021/Nyákterv/Jaras_nyak_3.png

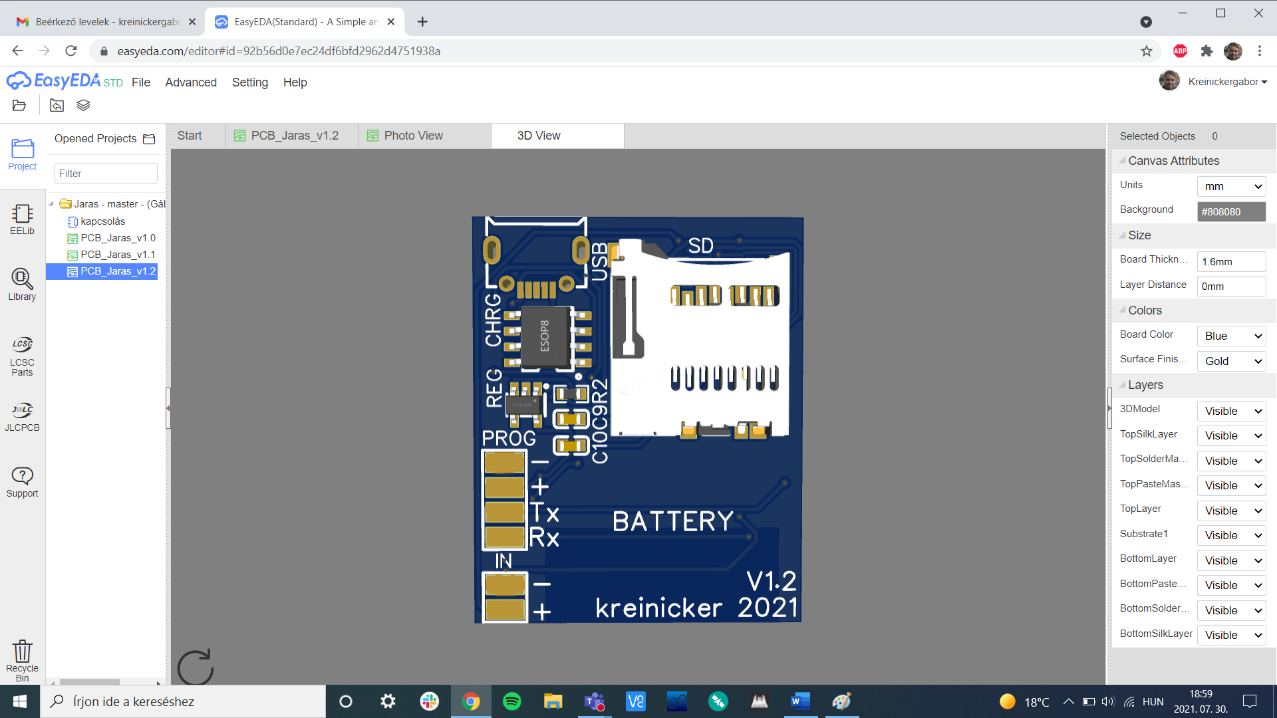
TDK 2021/Nyákterv/Jaras_nyak_3.png
