kreini/J-r-s/TDK 2021/Nyákterv/Jaras_nyak_4.png

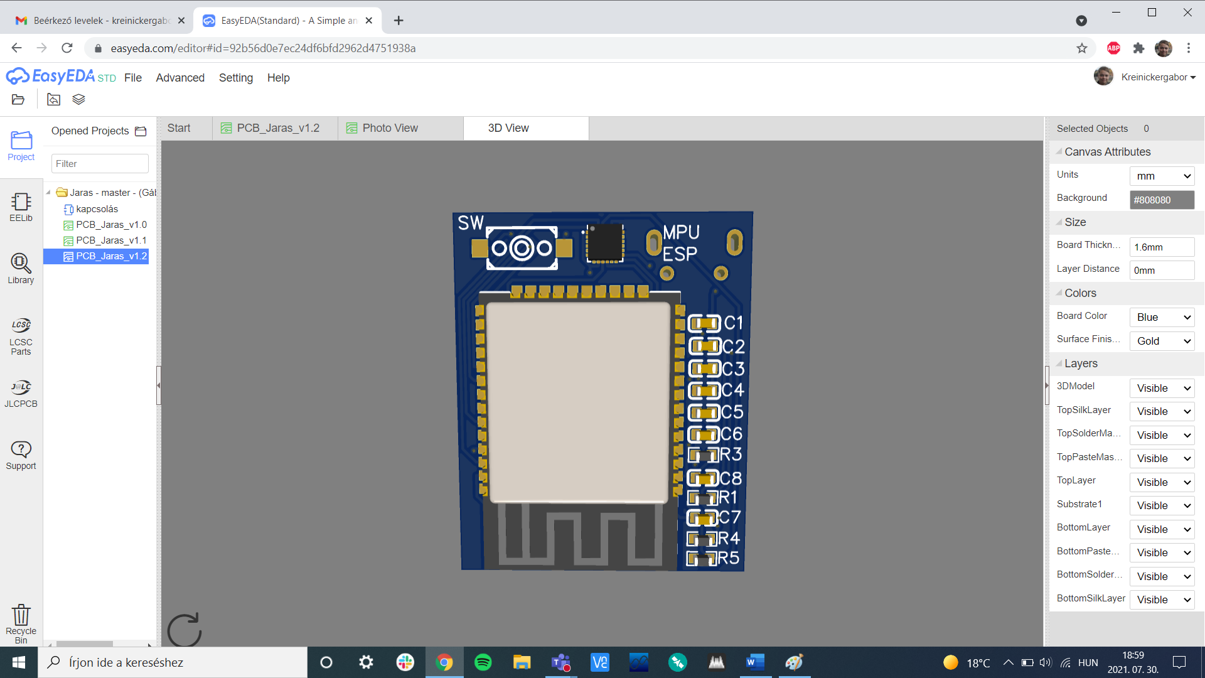
TDK 2021/Nyákterv/Jaras_nyak_4.png
