kreini/J-r-s/TDK 2021/Nyákterv/Jaras_nyak_6.png

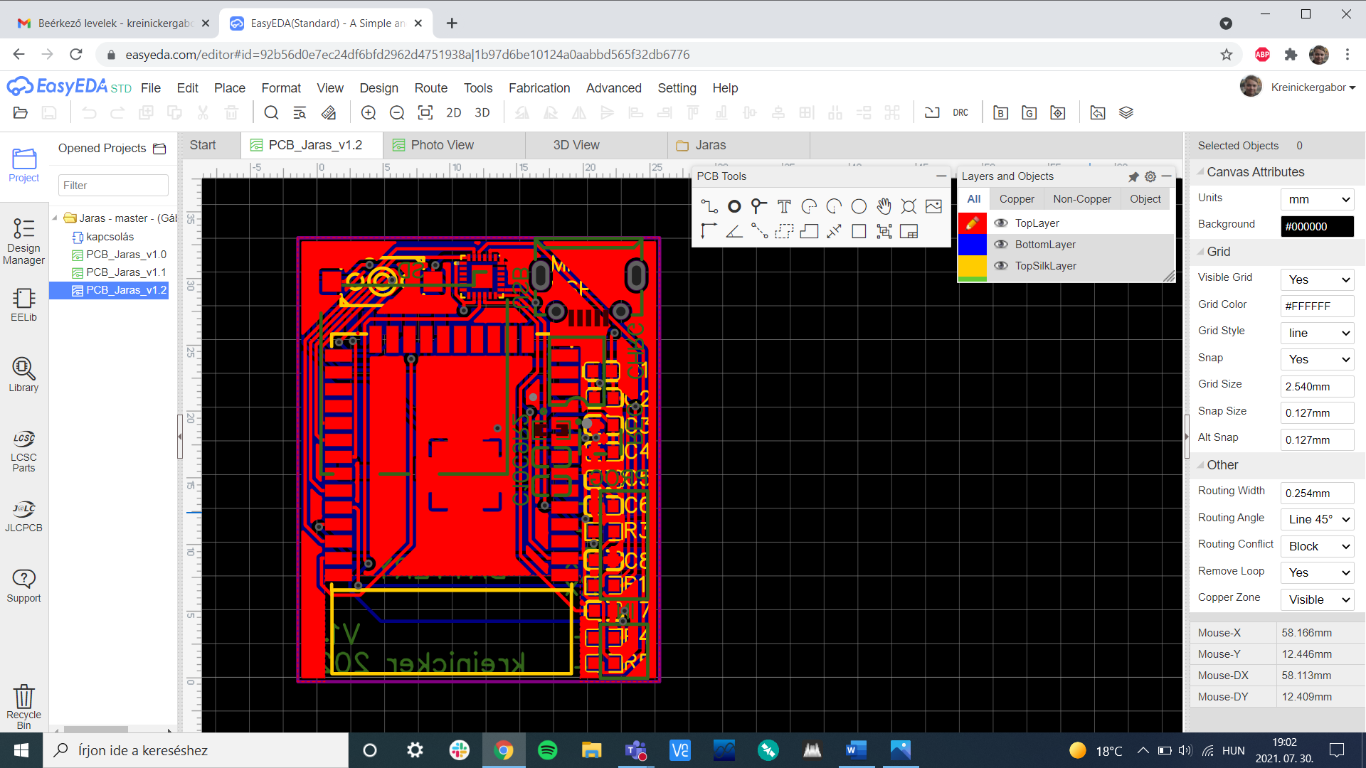
TDK 2021/Nyákterv/Jaras_nyak_6.png
