kreini/J-r-s/PosTracker/Pályamunka/Paint.net/Test.jpg

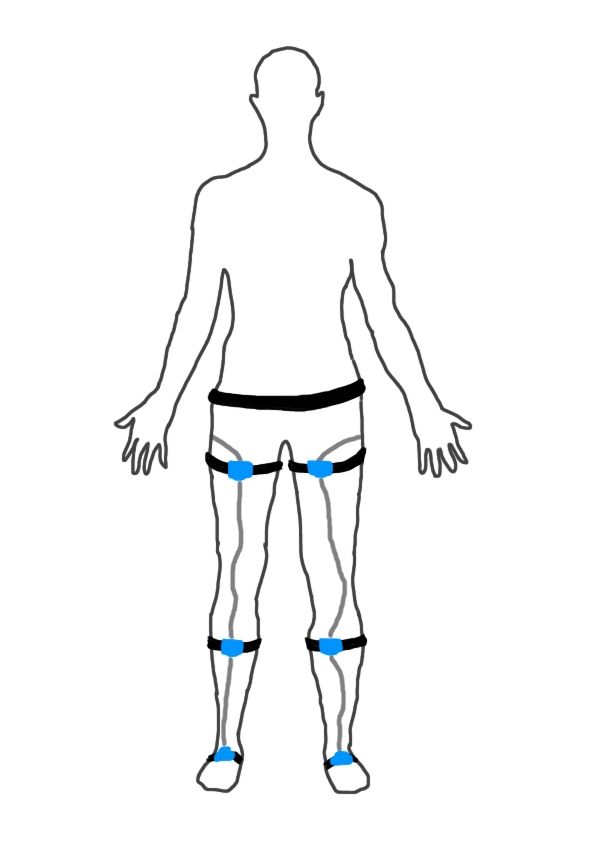
PosTracker/Pályamunka/Paint.net/Test.jpg
