kreini/J-r-s/PosTracker/Pályamunka/Műszaki rajzok/Szenzor ház.pdf

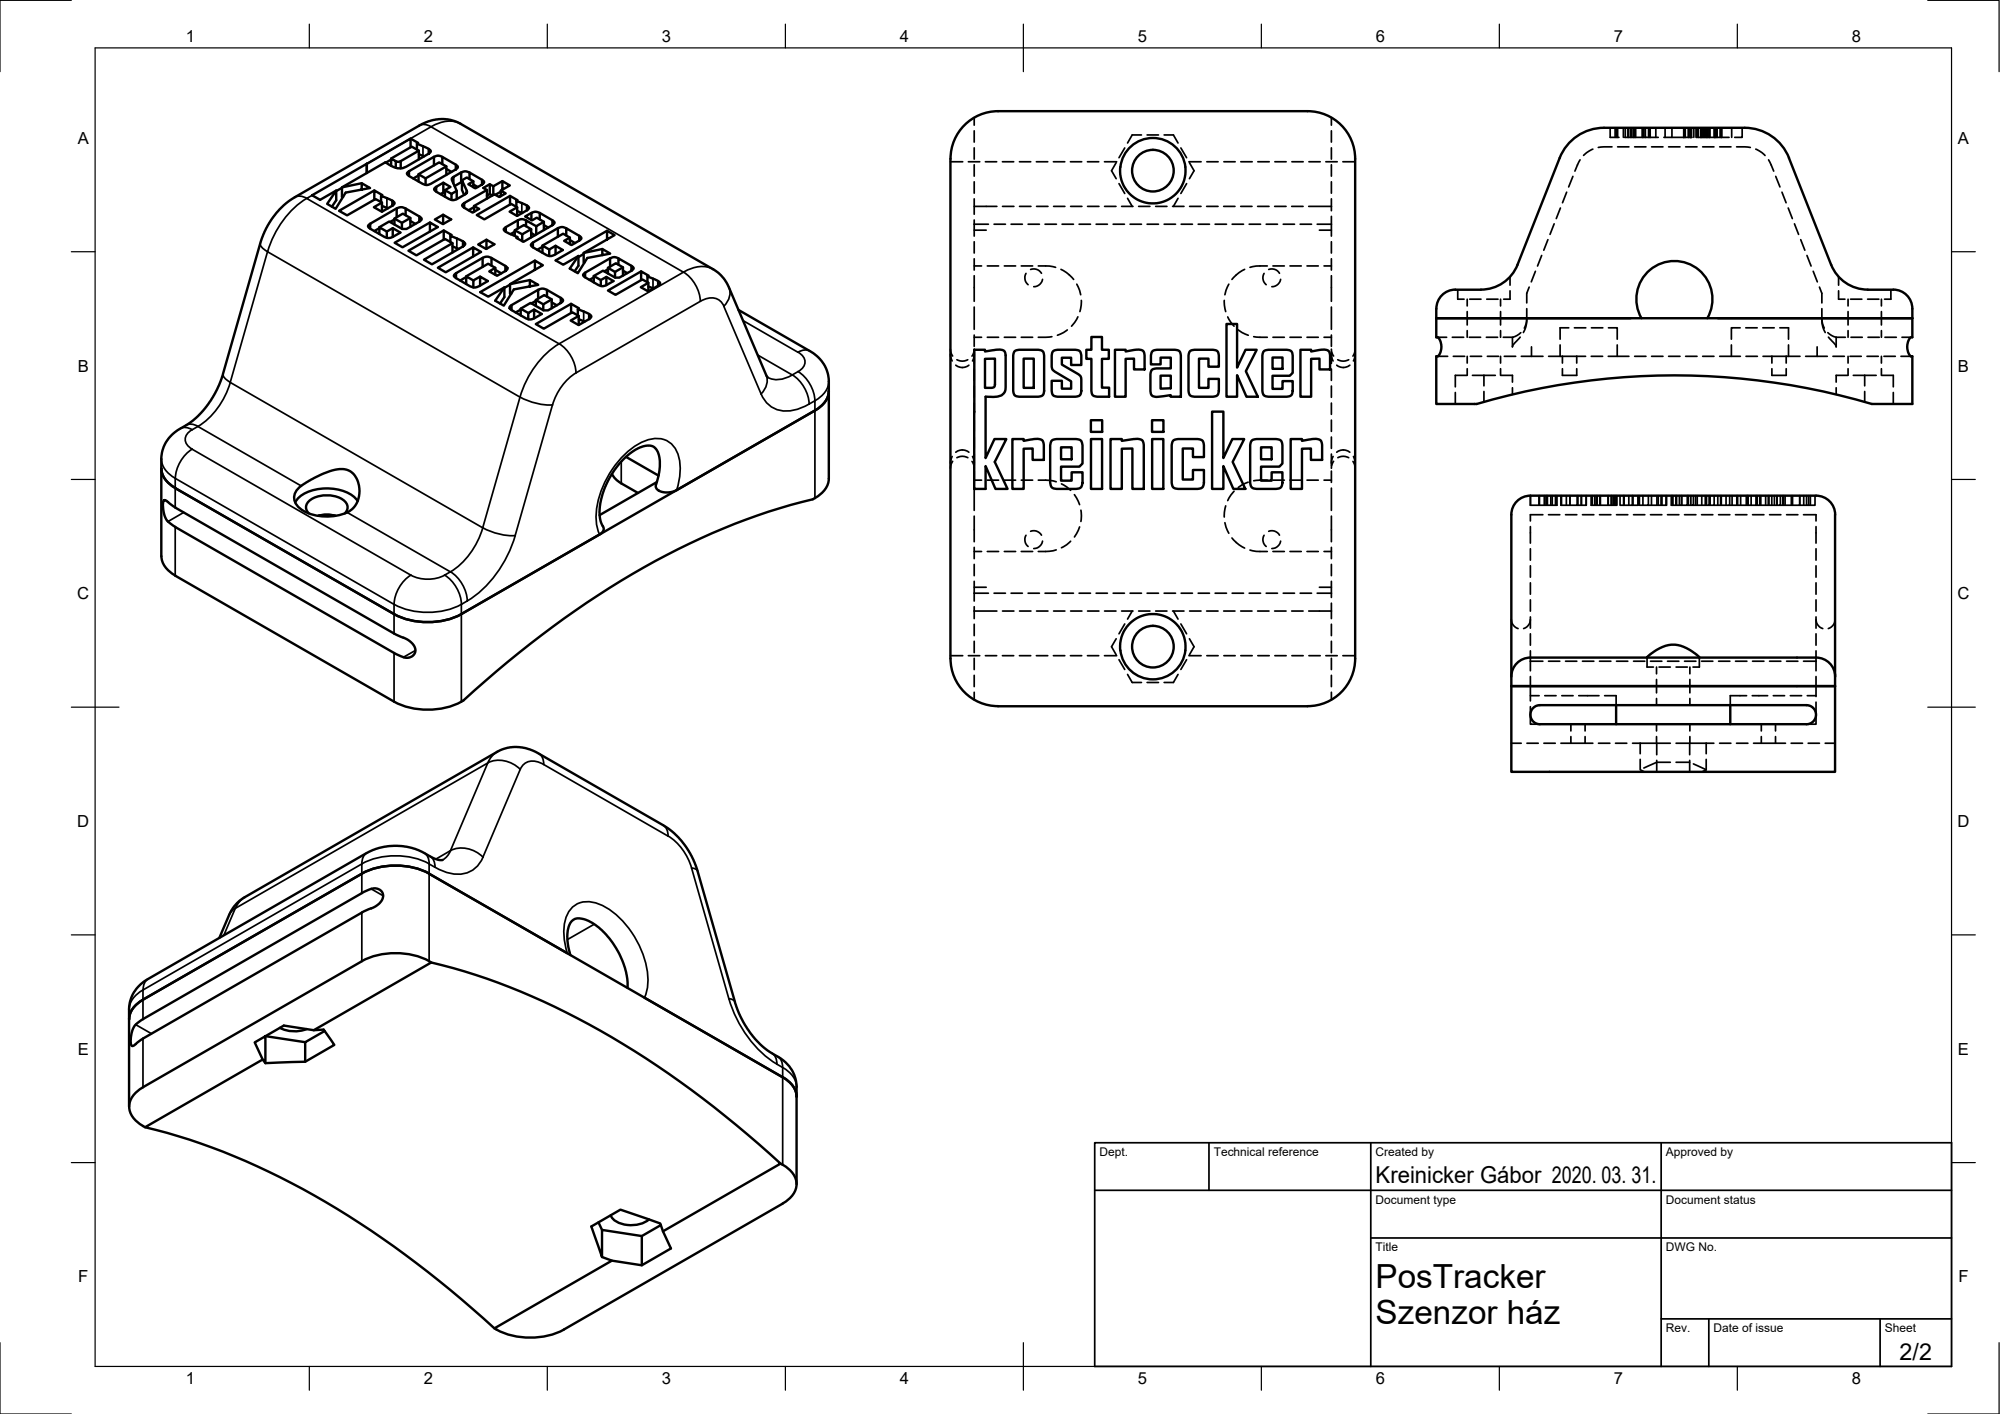
[picture p227: page 1]

Dept. | Technical reference | Created by Kreinicker Gábor 2020. 03. 31. | Approved by

Document type | Document status

Title PosTracker Szenzor ház | DWG No.

Rev. | Date of issue | Sheet 2/2
