kreini/J-r-s/PosTracker/Pályamunka/Műszaki rajzok/Vezérlő ház.pdf

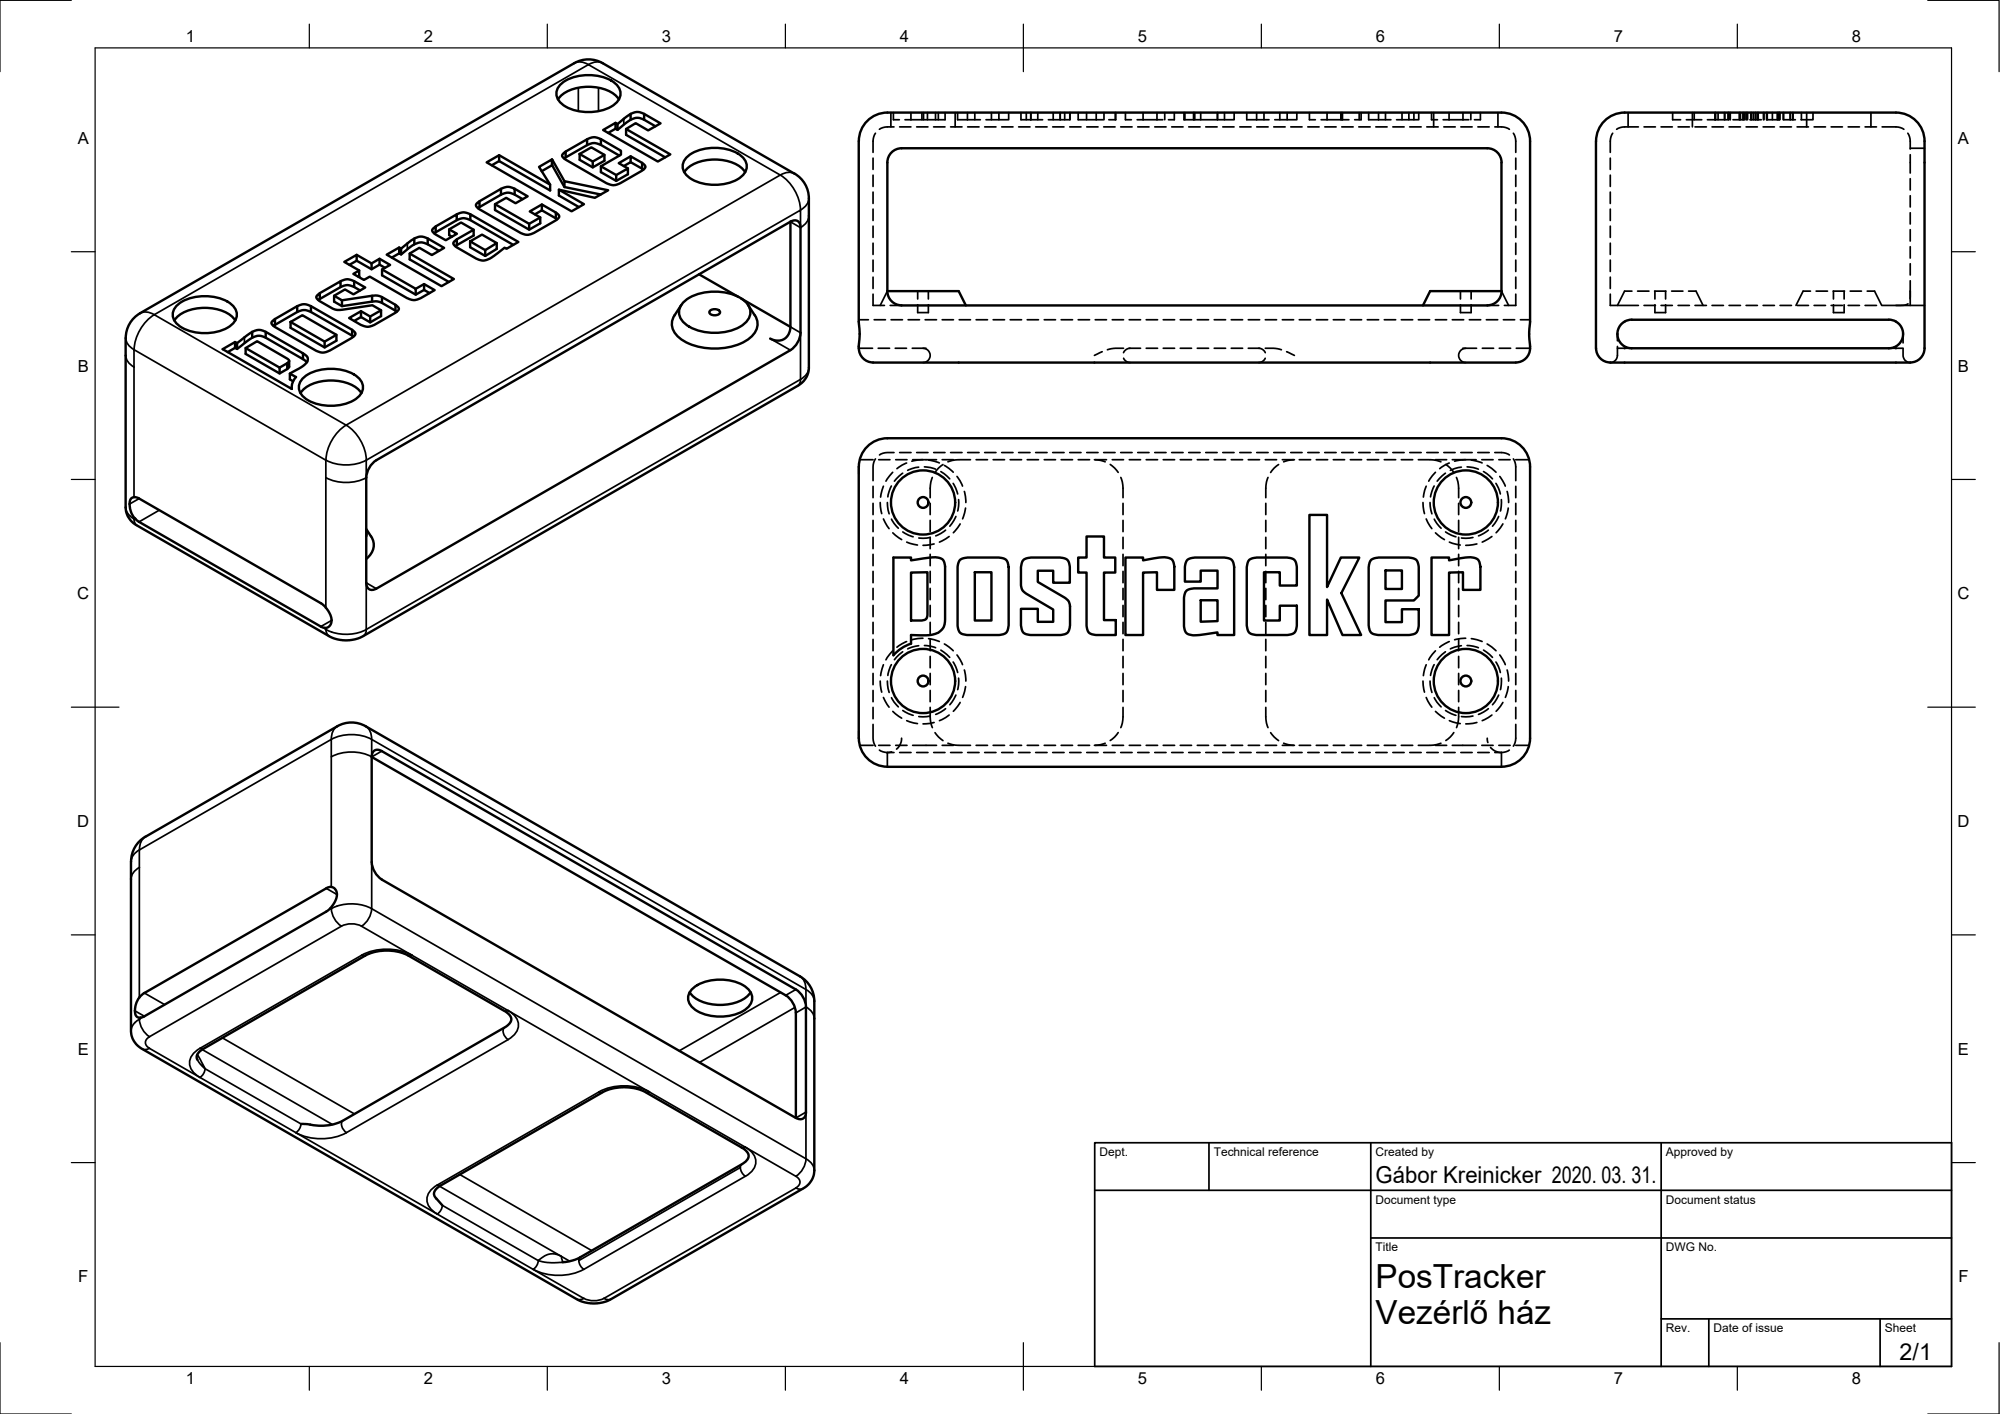
[picture p228: page 1]

Dept. | Technical reference | Created by Gábor Kreinicker 2020. 03. 31. | Approved by

Document type | Document status

Title PosTracker Vezérlő ház | DWG No.

Rev. | Date of issue | Sheet 2/1
