kreini/J-r-s/TDK 2021/Mérés/Hitelesítés/Infók.pdf

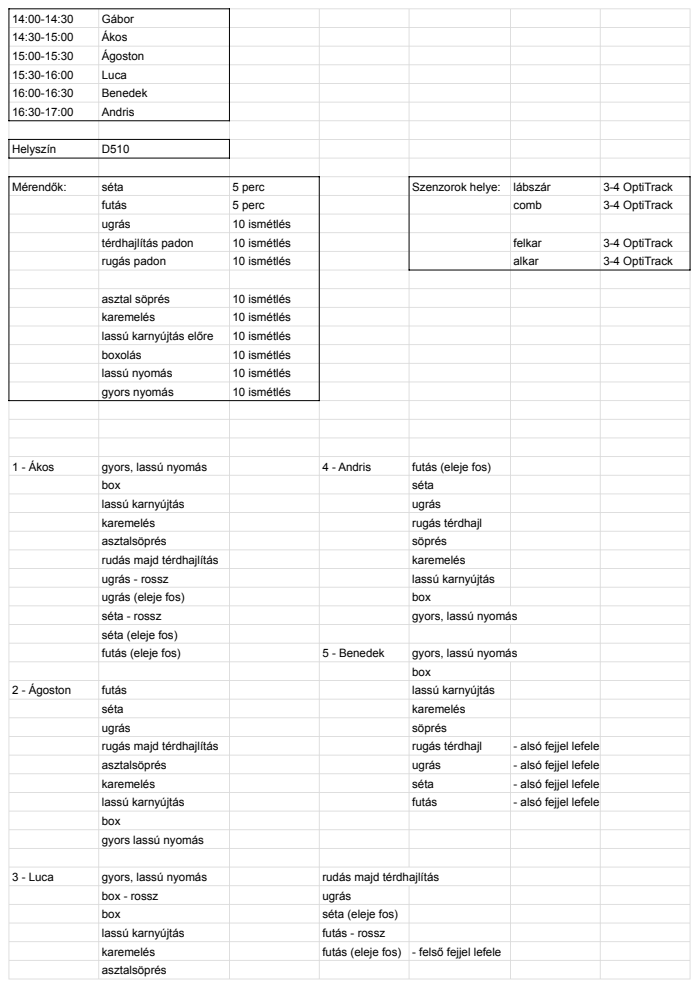
[picture p229: page 1]
Gábor; Ákos; Ágoston; Luca; Benedek; Andris; Helyszín; Mérendők:; séta; 5 perc; Szenzorok helye: lábszár; 3-4 OptiTrack; futás; comb; ugrás; 10 ismétlés; térdhajlítás padon; felkar; rugás padon; alkar; asztal söprés; karemelés; lassú karnyújtás előre; boxolás; lassú nyomás; gyors nyomás; 1 - Ákos; gyors, lassú nyomás; 4 - Andris; futás (eleje fos); box; lassú karnyújtás; rugás térdhajl; asztalsöprés; söprés; rudás majd térdhajlítás; ugrás - rossz; ugrás (eleje fos); séta - rossz; 5 - Benedek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

séta (eleje fos)

box
gyors lassú nyomás
