kreini/J-r-s/pályázatok/ÚNKP/2021-22/Neptun igazolas.pdf

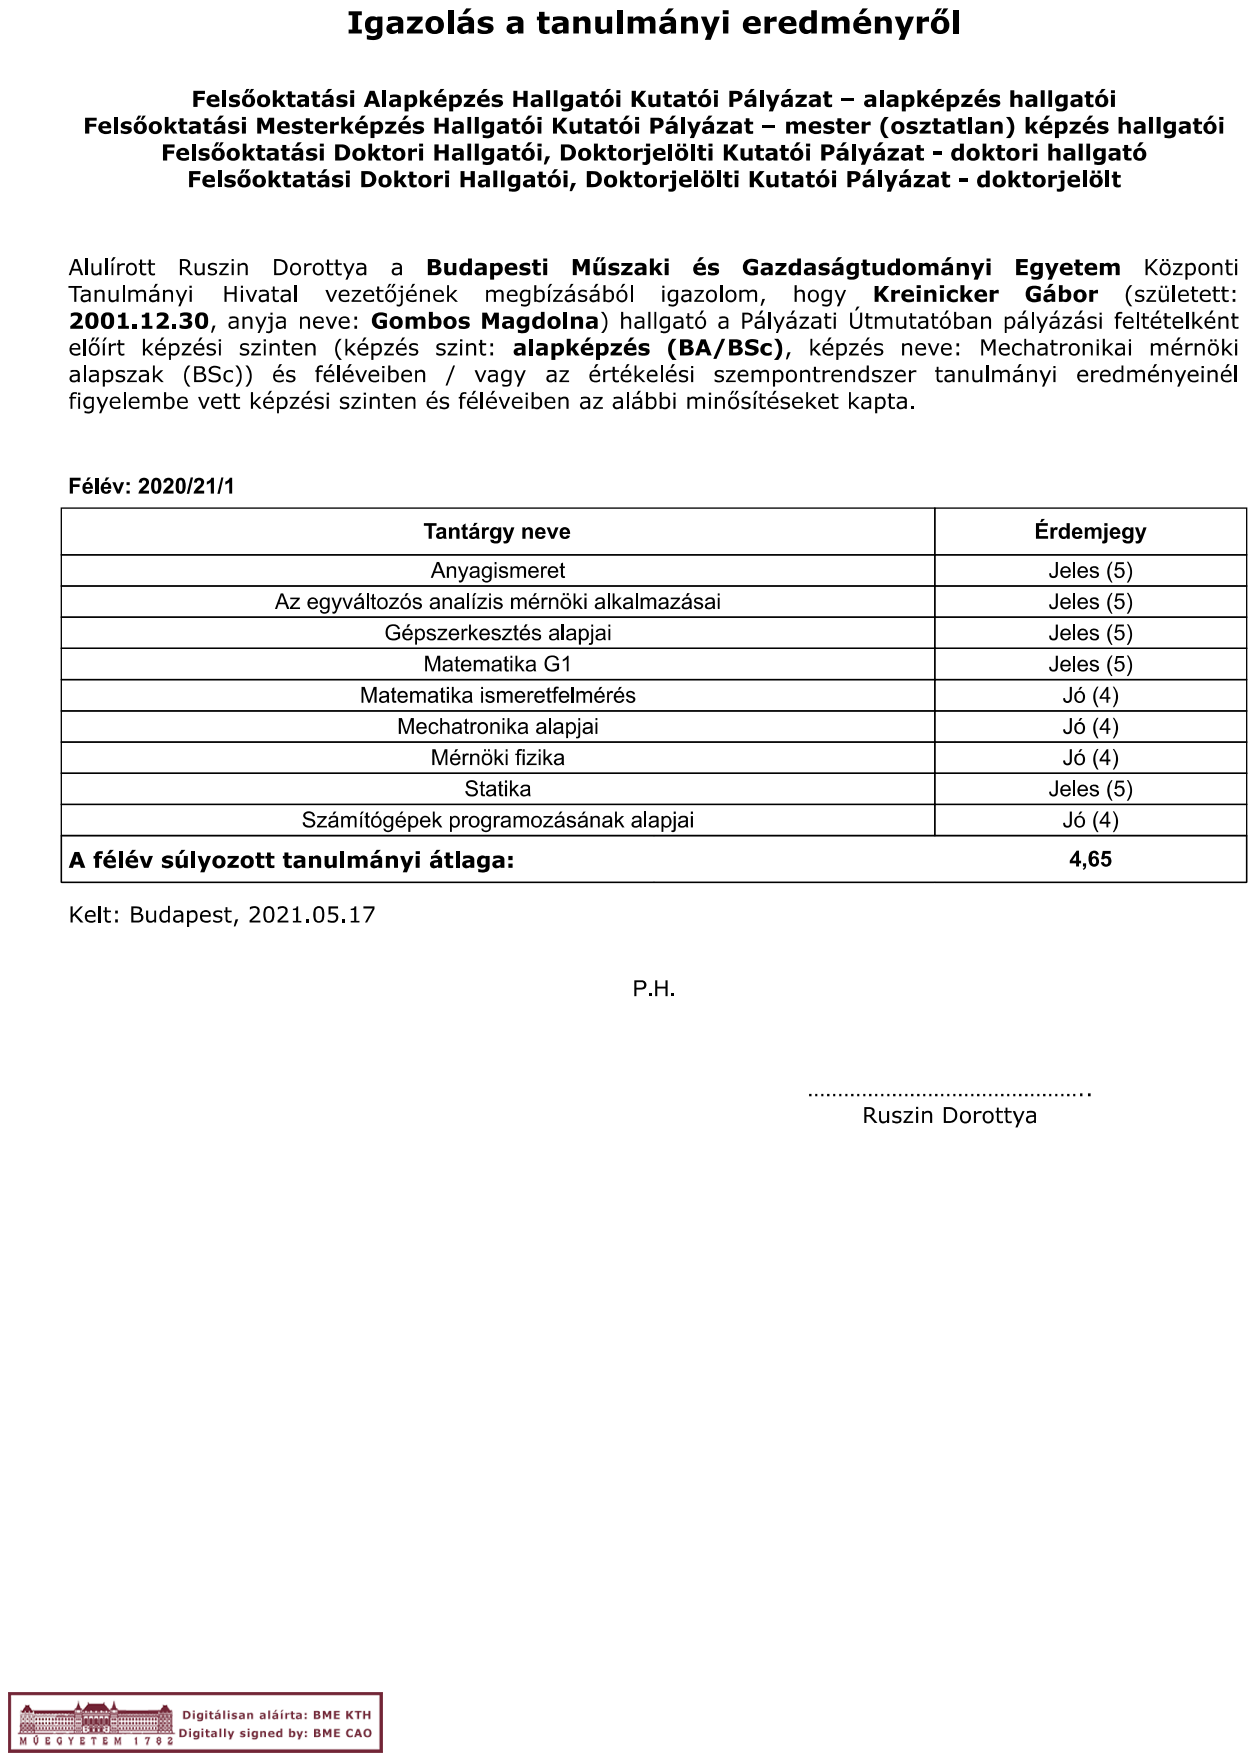
[picture p230: page 1]
