kreini/J-r-s/PosTracker/Kódok/Arduino/SOTE/sketch_feb02a/sketch_feb02a.ino

#include "MPU9250.h"

// an MPU9250 object with the MPU-9250 sensor on I2C bus 0 with address 0x68
MPU9250 IMU(Wire,0x68);
int status;

void setup() {
  // serial to display data
  Serial.begin(115200);
  while(!Serial) {}

  // start communication with IMU 
  status = IMU.begin();
  if (status < 0) {
    Serial.println("IMU initialization unsuccessful");
    Serial.println("Check IMU wiring or try cycling power");
    Serial.print("Status: ");
    Serial.println(status);
    while(1) {}
    
  }
  IMU.setSrd(1);
  delay(10);
}

void loop() {
  IMU.readSensor();

  // display the data
  Serial.print(IMU.getAccelX_mss(),6);
  Serial.print(",");
  Serial.print(IMU.getAccelY_mss(),6);
  Serial.print(",");
  Serial.print(IMU.getAccelZ_mss(),6);
  Serial.print(",");
  Serial.print(IMU.getGyroX_rads(),6);
  Serial.print(",");
  Serial.print(IMU.getGyroY_rads(),6);
  Serial.print(",");
  Serial.print(IMU.getGyroZ_rads(),6);
  Serial.print("\n");
}
